impatrq/cnc_drawing_machine/boton de parada de emergencia/WhatsApp Image 2023-11-23 at 18.12.33.jpeg

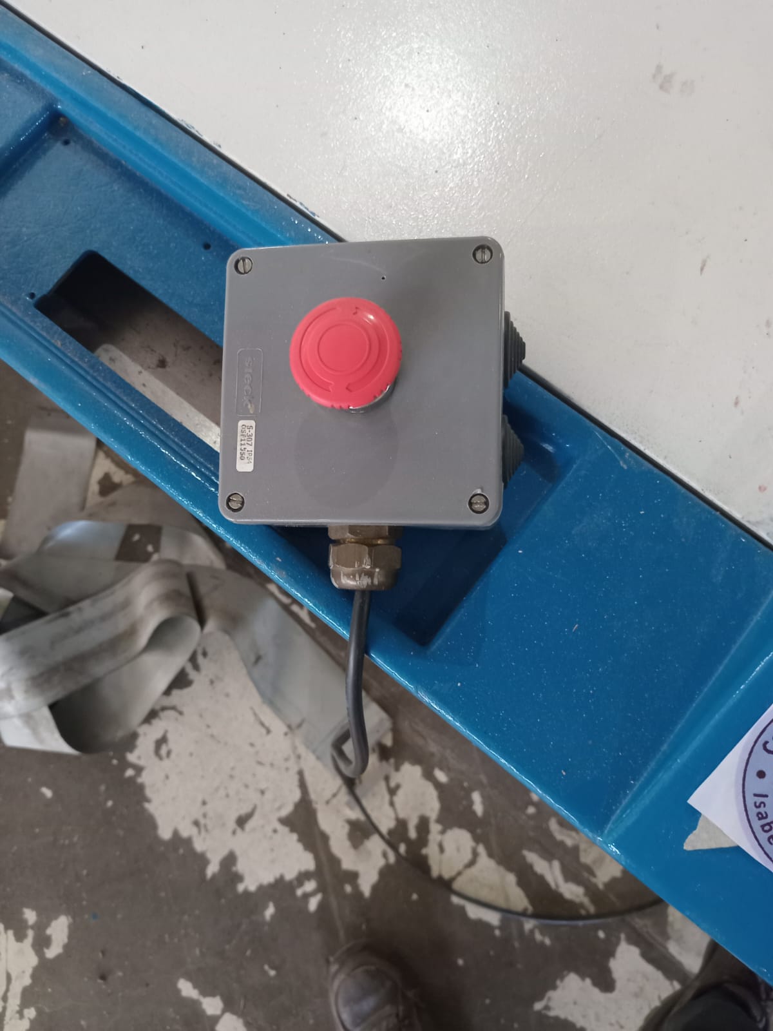
boton de parada de emergencia/WhatsApp Image 2023-11-23 at 18.12.33.jpeg
