impatrq/cnc_drawing_machine/Cortes y Grabados/cartel-zanik-mining.jpg

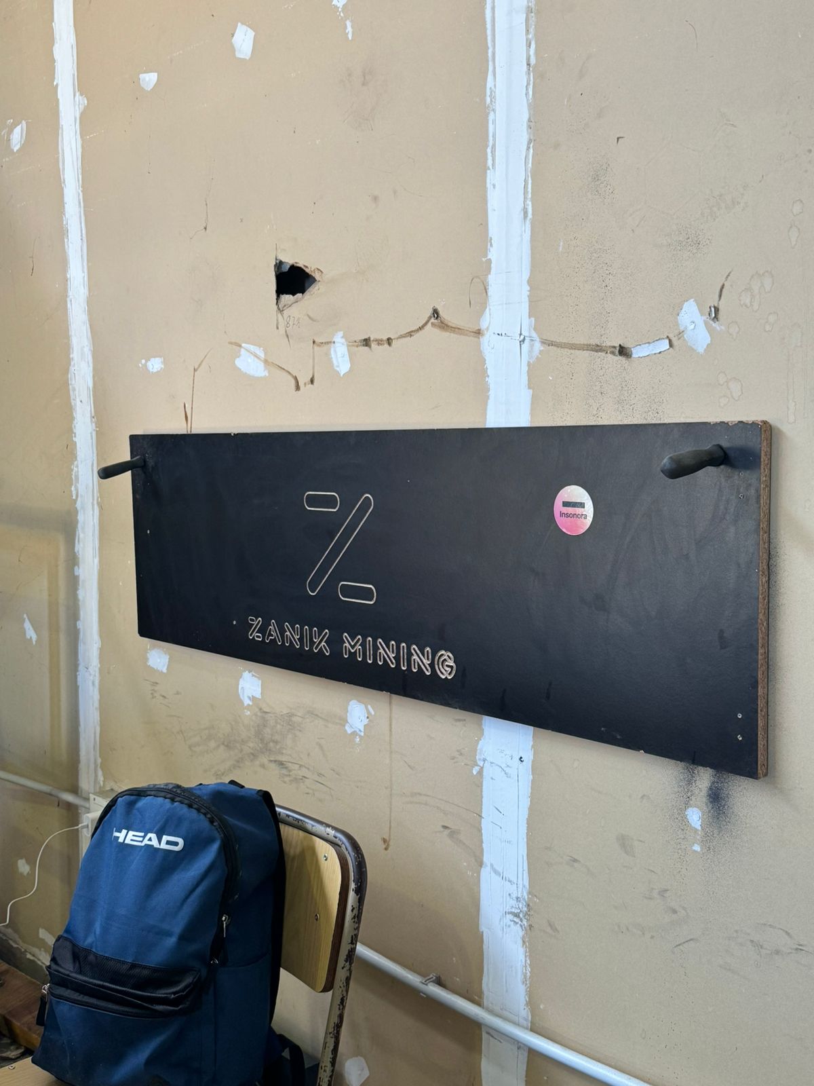
Cortes y Grabados/cartel-zanik-mining.jpg
