impatrq/cnc_drawing_machine/Cortes y Grabados/fluminense.jpg

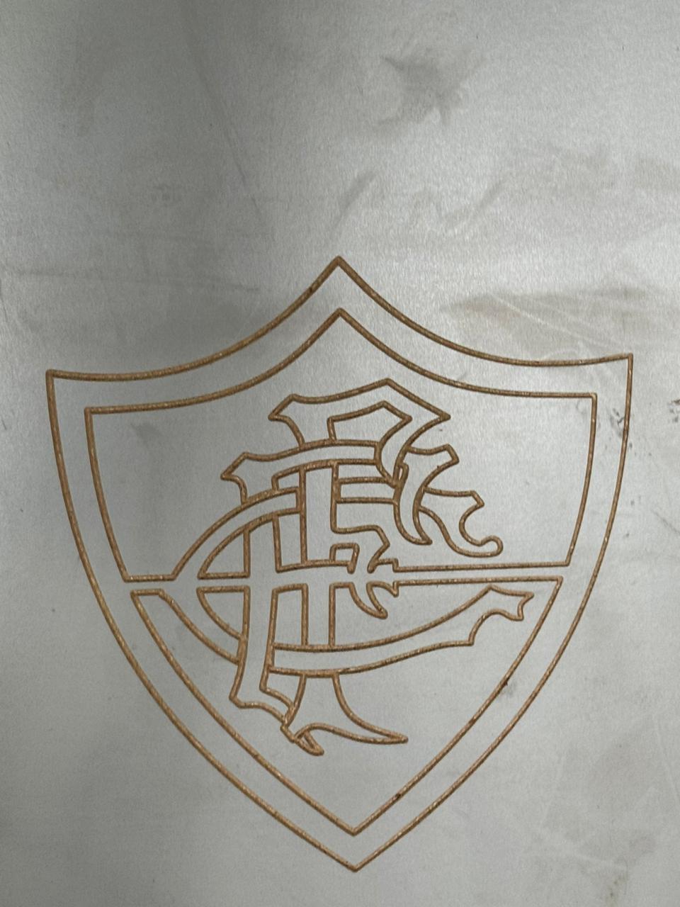
Cortes y Grabados/fluminense.jpg
