impatrq/cnc_drawing_machine/Cortes y Grabados/independiente .jpg

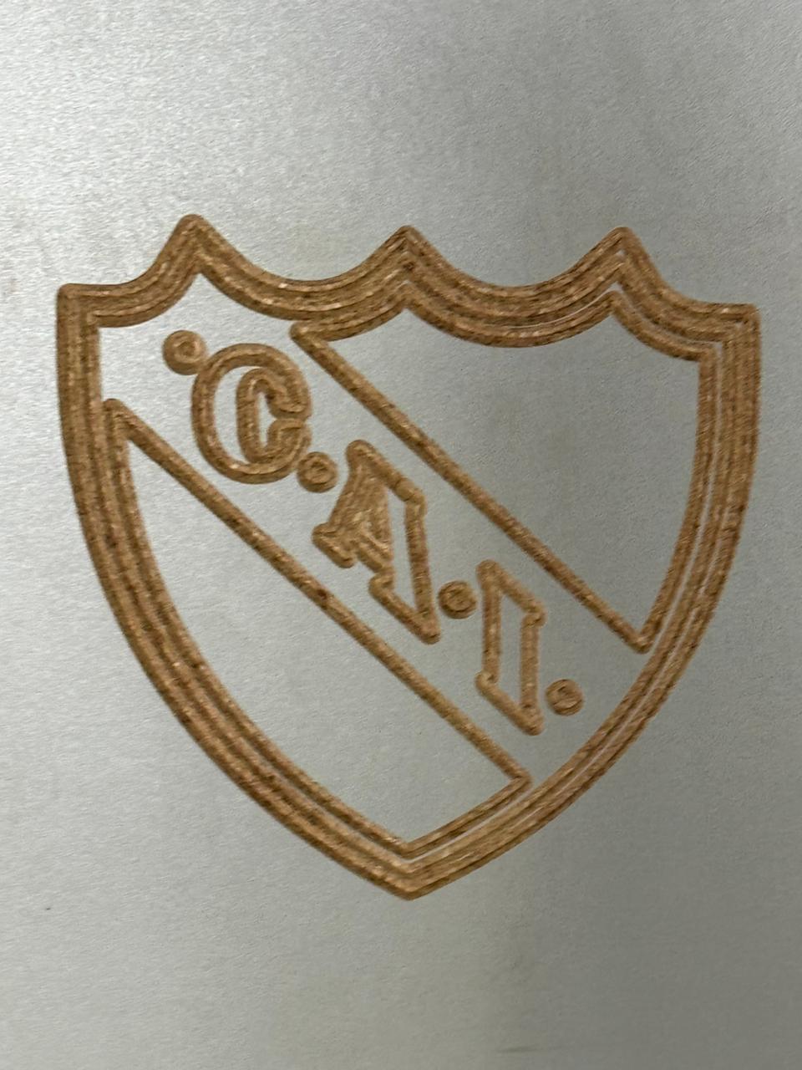
Cortes y Grabados/independiente .jpg
