impatrq/cnc_drawing_machine/Cortes y Grabados/mariposa.jpg

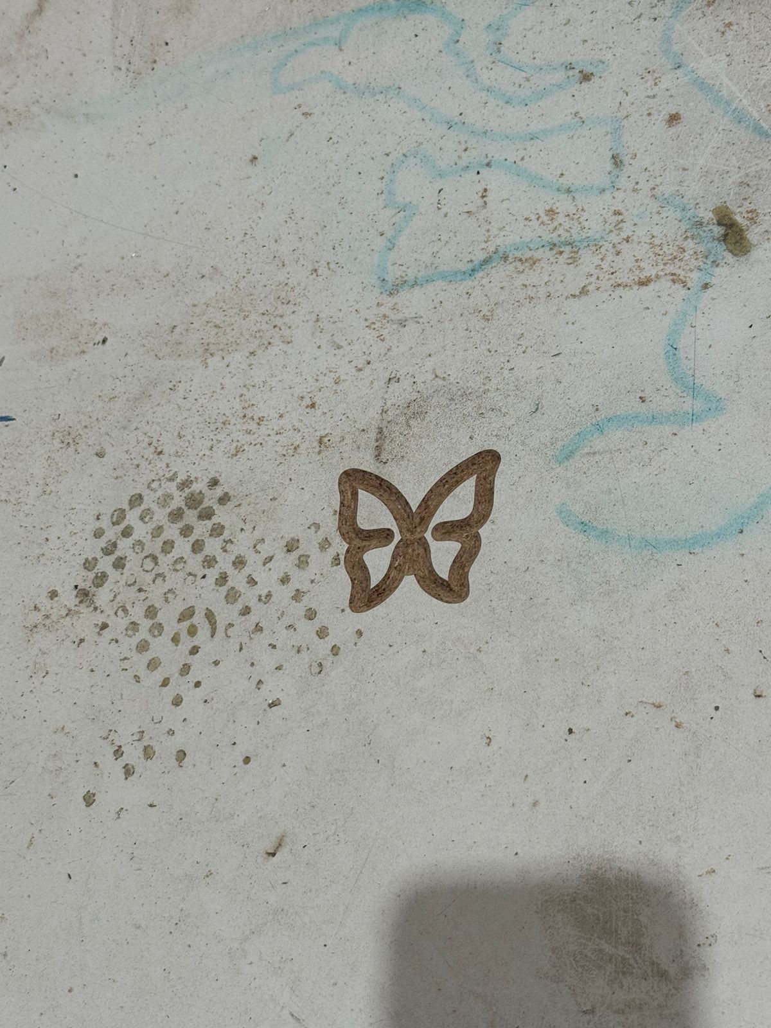
Cortes y Grabados/mariposa.jpg
