impatrq/cnc_drawing_machine/Cortes y Grabados/messi.jpg

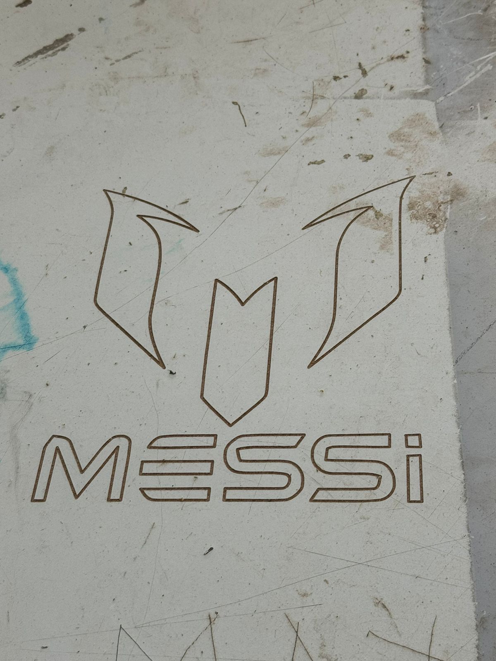
Cortes y Grabados/messi.jpg
