impatrq/cnc_drawing_machine/Cortes y Grabados/munay.jpg

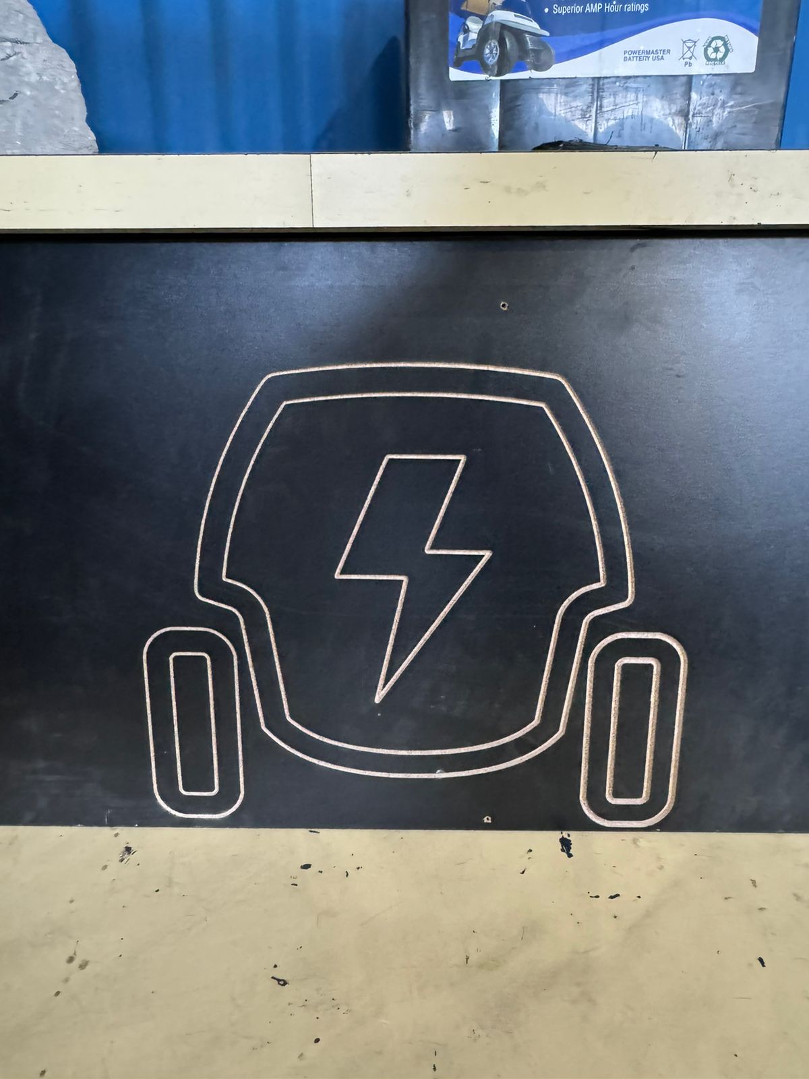
Cortes y Grabados/munay.jpg
