impatrq/cnc_drawing_machine/Cortes y Grabados/rick.jpg

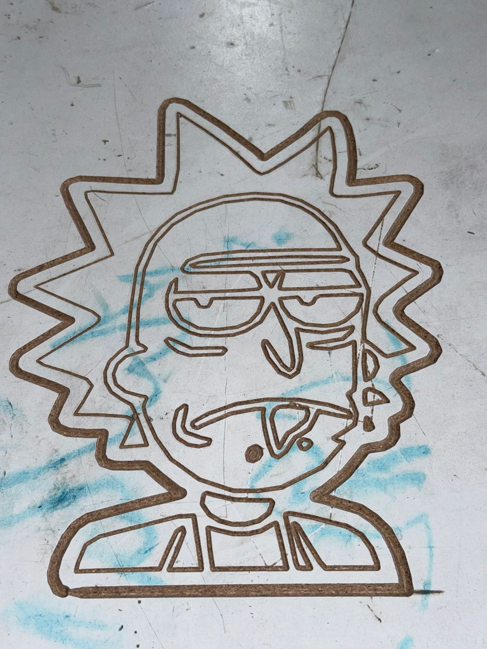
Cortes y Grabados/rick.jpg
