impatrq/cnc_drawing_machine/Cortes y Grabados/sonic.jpg

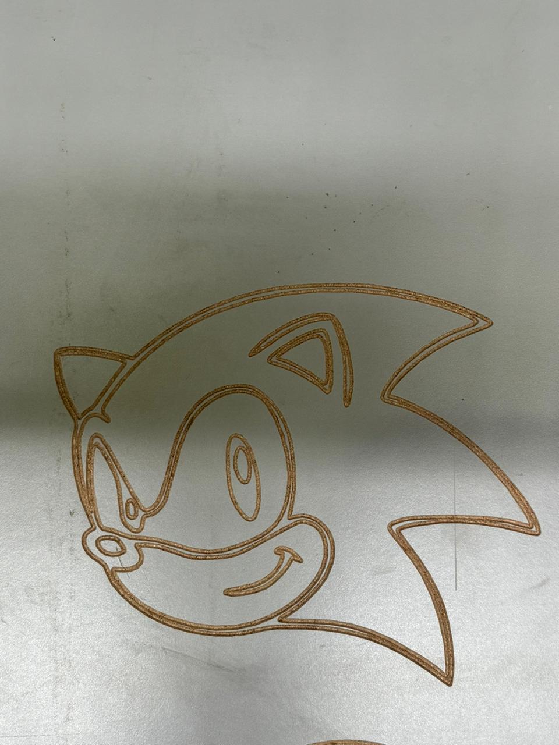
Cortes y Grabados/sonic.jpg
