impatrq/cnc_drawing_machine/Driver Modular/Driver Modular Tb6600 Settings.jpg

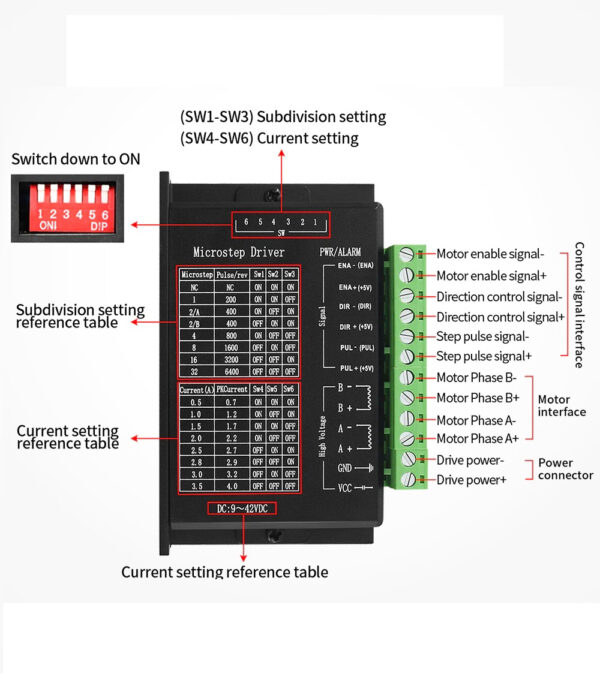
Driver Modular/Driver Modular Tb6600 Settings.jpg
