impatrq/cnc_drawing_machine/Driver Modular/Driver Modular Tb6600.png

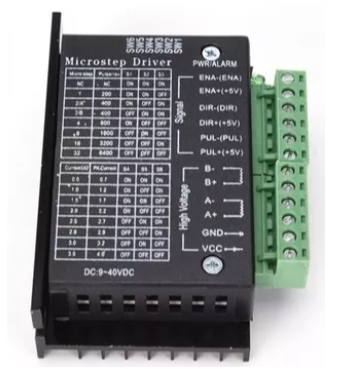
Driver Modular/Driver Modular Tb6600.png
