impatrq/cnc_drawing_machine/Driver Modular/drivers.jpg

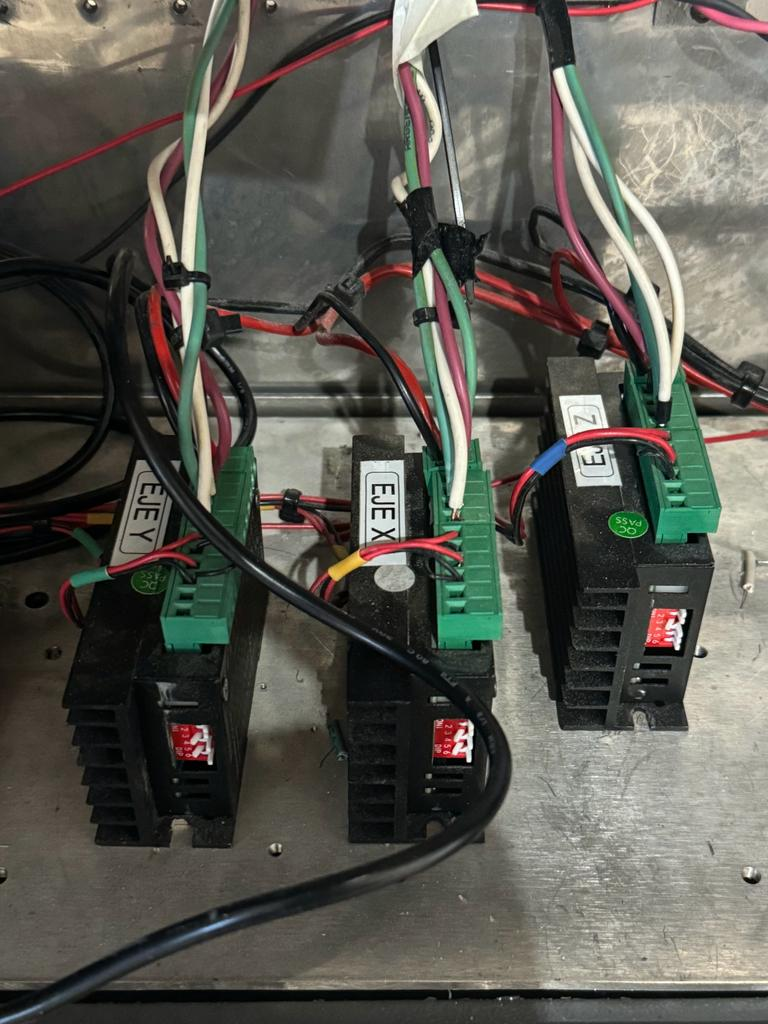
Driver Modular/drivers.jpg
