impatrq/cnc_drawing_machine/Eje X/Eje X conectado a su soporte.jpeg

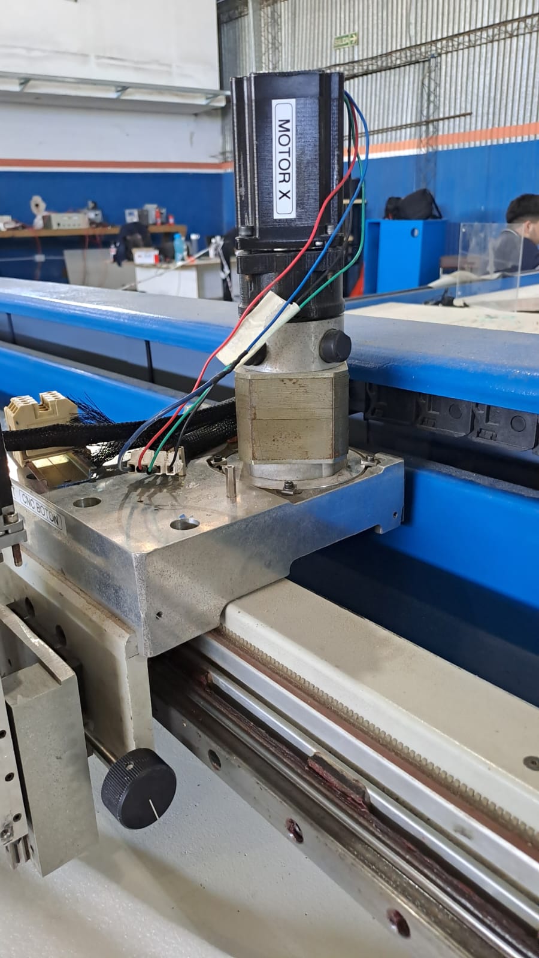
Eje X/Eje X conectado a su soporte.jpeg
