impatrq/cnc_drawing_machine/Eje X/Vista de lado del driver del Eje X.jpeg

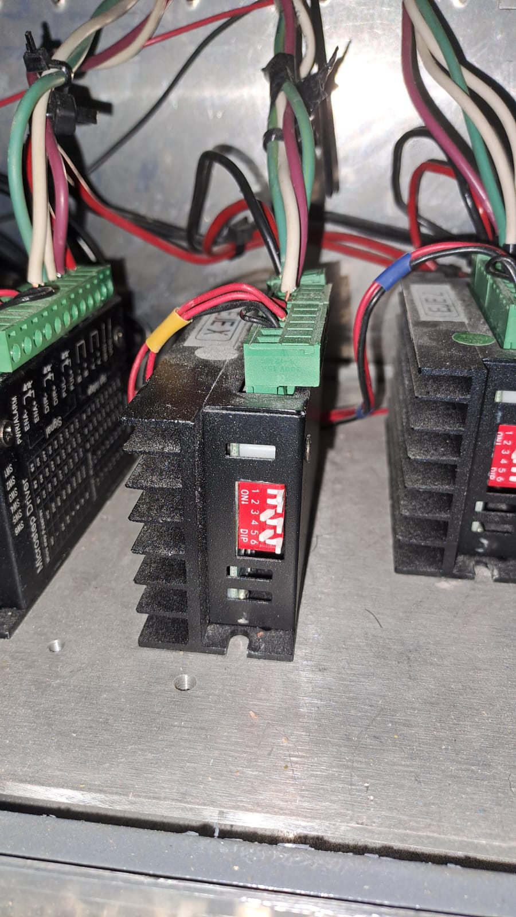
Eje X/Vista de lado del driver del Eje X.jpeg
