impatrq/cnc_drawing_machine/eje y/WhatsApp Image 2023-11-23 at 18.12.32 (1).jpeg

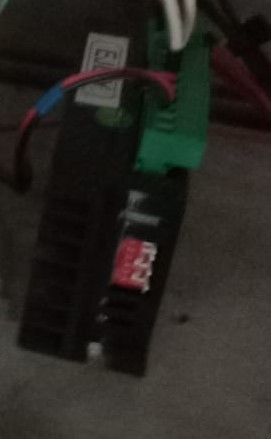
eje y/WhatsApp Image 2023-11-23 at 18.12.32 (1).jpeg
