impatrq/cnc_drawing_machine/eje y/WhatsApp Image 2023-11-24 at 00.11.37.jpeg

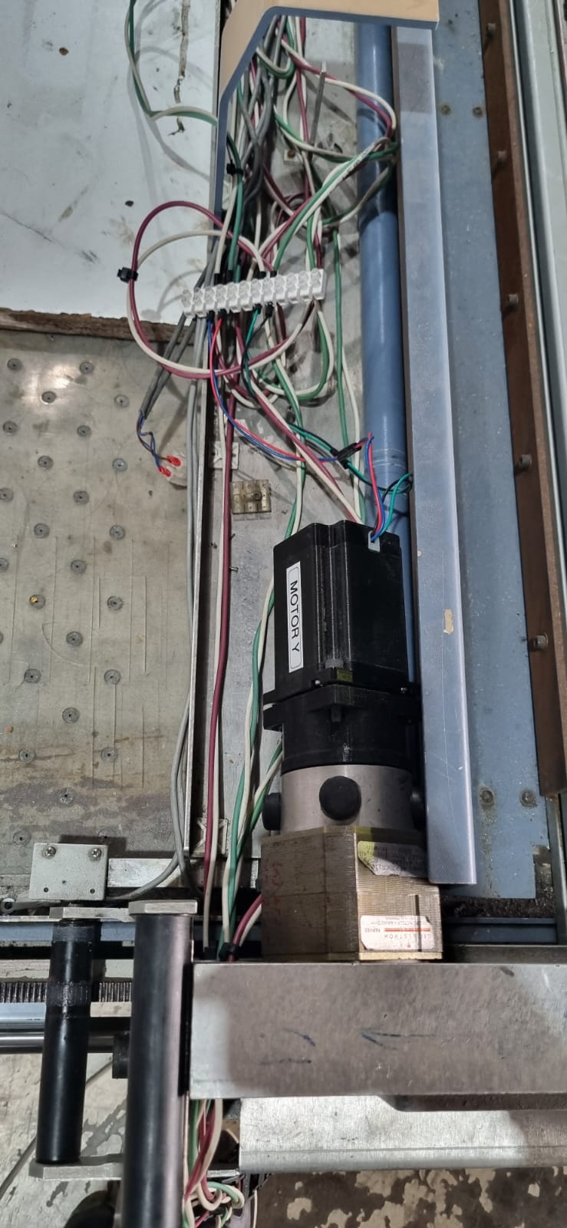
eje y/WhatsApp Image 2023-11-24 at 00.11.37.jpeg
