impatrq/cnc_drawing_machine/eje z/d.jpg

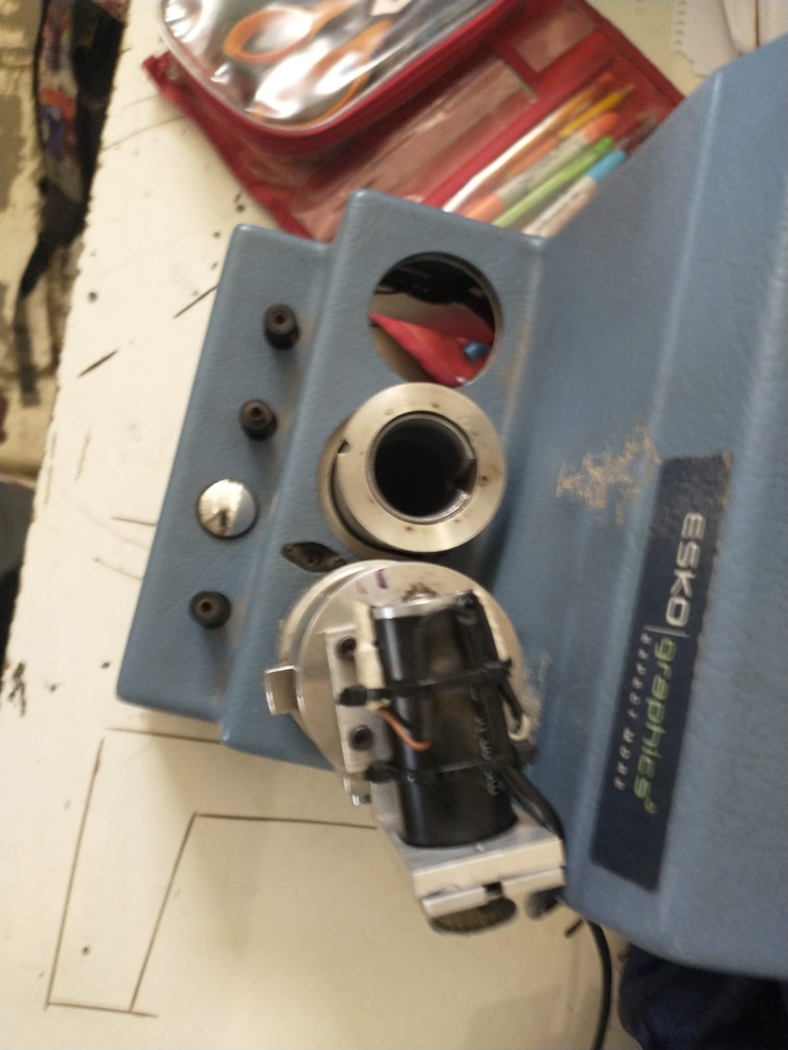
eje z/d.jpg
