impatrq/cnc_drawing_machine/eje z/parte movil eje z.PNG

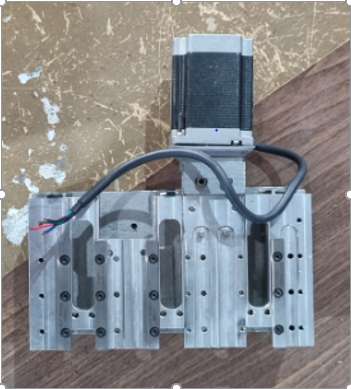
eje z/parte movil eje z.PNG
