impatrq/cnc_drawing_machine/eje z/WhatsApp Image 2023-11-23 at 18.12.32 (2).jpeg

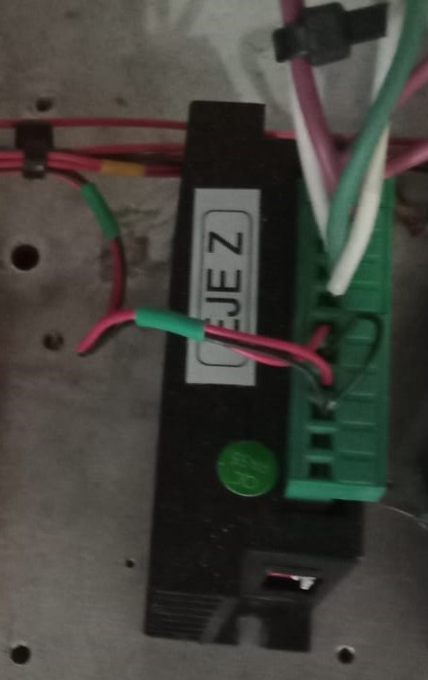
eje z/WhatsApp Image 2023-11-23 at 18.12.32 (2).jpeg
