impatrq/cnc_drawing_machine/eje z/WhatsApp Image 2023-11-24 at 00.47.14.jpeg

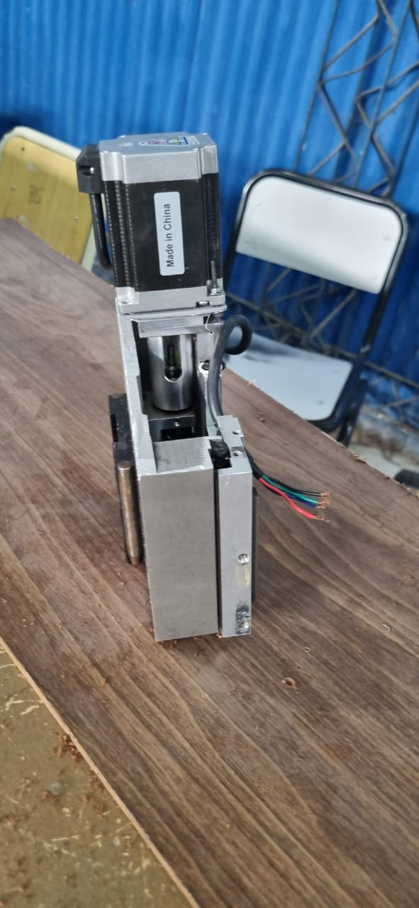
eje z/WhatsApp Image 2023-11-24 at 00.47.14.jpeg
