impatrq/cnc_drawing_machine/Esquema eléctrico del CNC/Esquema de CNC.jpg

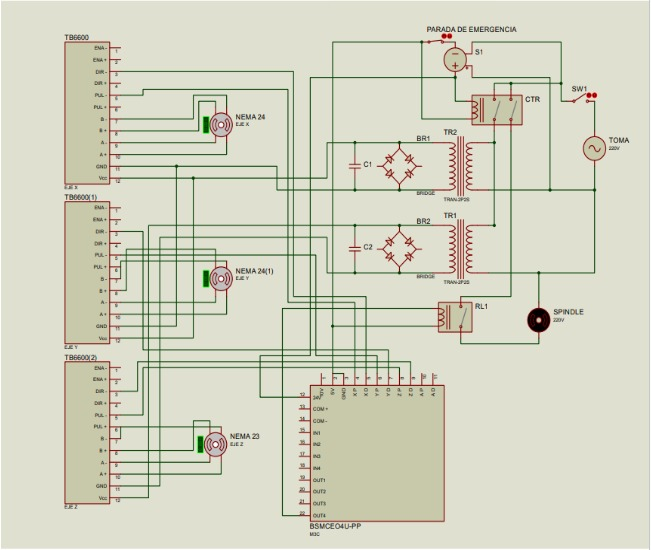
Esquema eléctrico del CNC/Esquema de CNC.jpg
