impatrq/cnc_drawing_machine/Esquema eléctrico del CNC/WhatsApp Image 2023-11-23 at 23.42.56 (1).jpeg

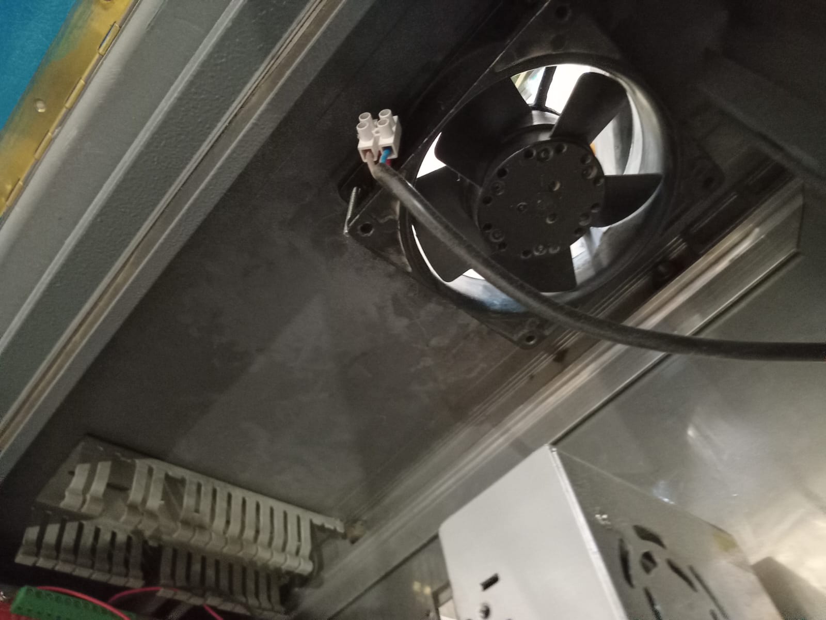
Esquema eléctrico del CNC/WhatsApp Image 2023-11-23 at 23.42.56 (1).jpeg
