impatrq/cnc_drawing_machine/Facturacion/Factura 1.png

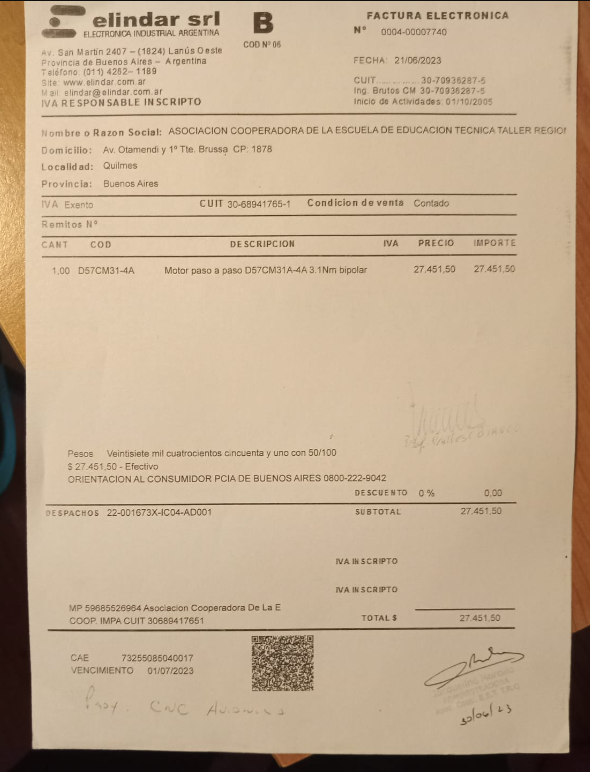
Facturacion/Factura 1.png
