impatrq/cnc_drawing_machine/Facturacion/Factura 2.png

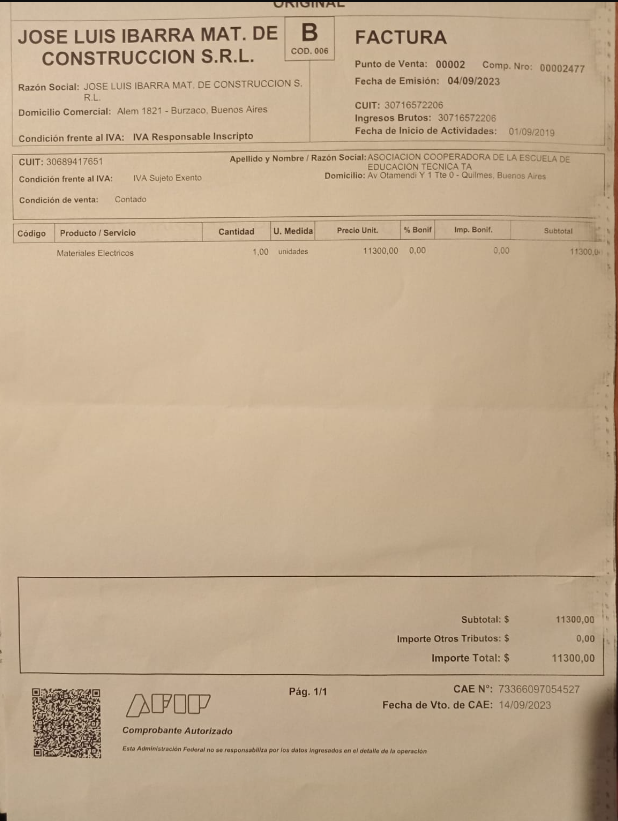
Facturacion/Factura 2.png
