impatrq/cnc_drawing_machine/Facturacion/Presupuesto 1.png

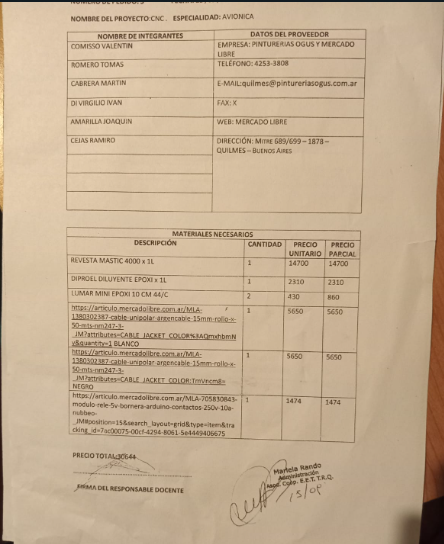
Facturacion/Presupuesto 1.png
