impatrq/cnc_drawing_machine/Facturacion/Presupuesto 2.png

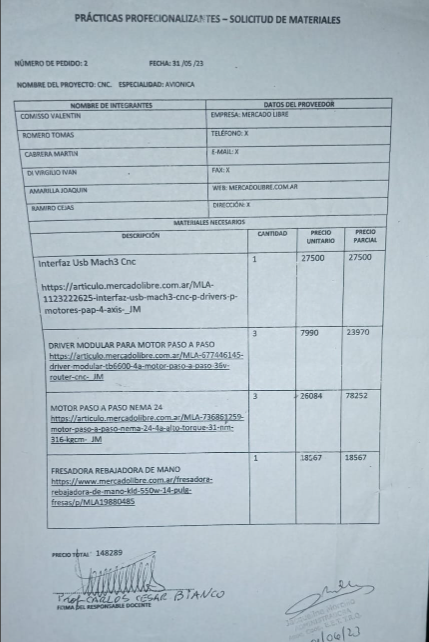
Facturacion/Presupuesto 2.png
