impatrq/cnc_drawing_machine/Facturacion/Presupuesto 3.png

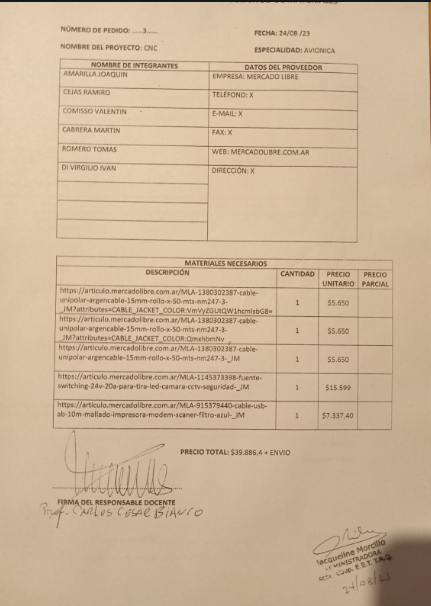
Facturacion/Presupuesto 3.png
