impatrq/cnc_drawing_machine/Fresadora/config_fresadora.PNG

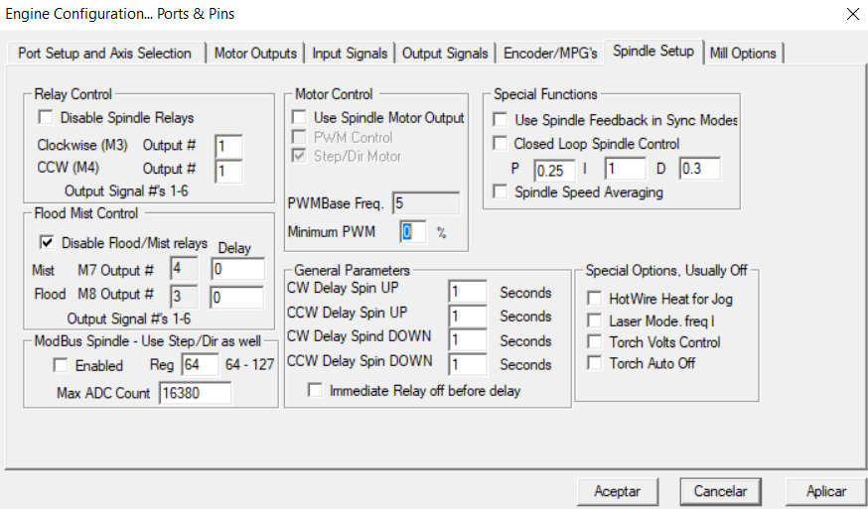
Fresadora/config_fresadora.PNG
