impatrq/cnc_drawing_machine/Fresadora/pins_fresadora.PNG

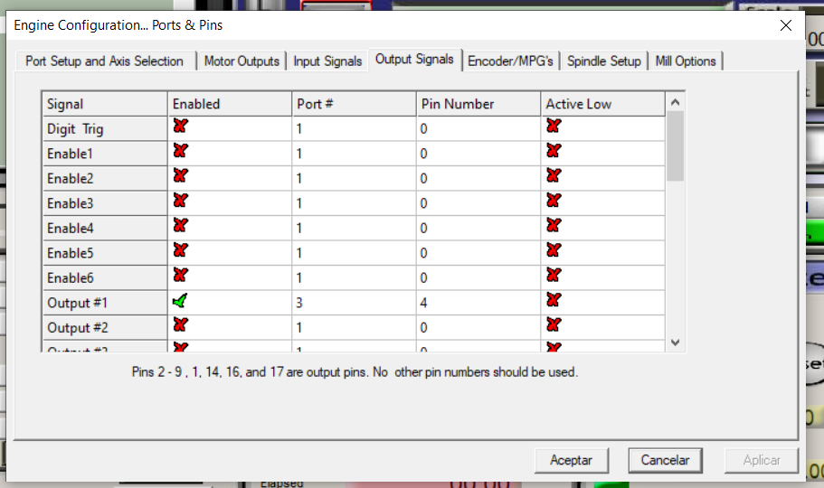
Fresadora/pins_fresadora.PNG
