impatrq/cnc_drawing_machine/Fresadora/rele y contactor.jpeg

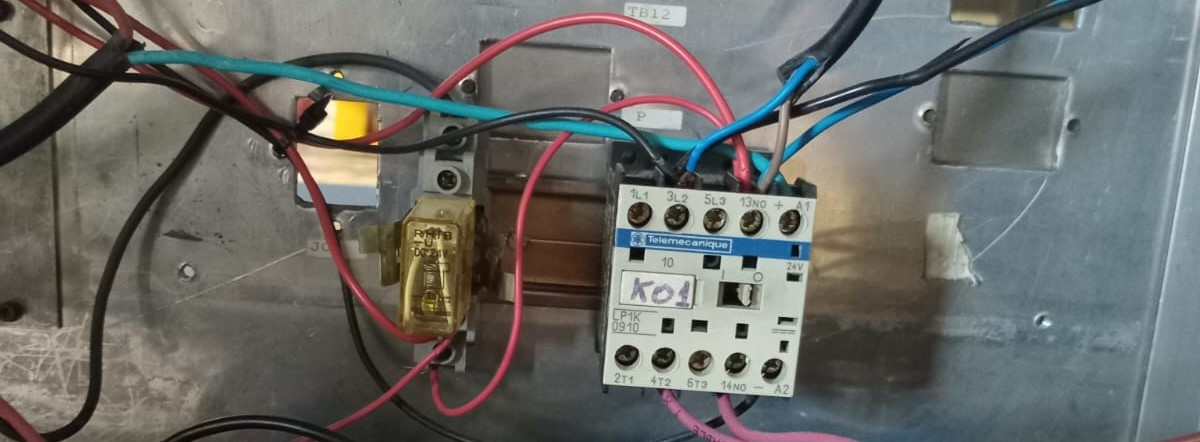
Fresadora/rele y contactor.jpeg
