impatrq/cnc_drawing_machine/Fresadora/WhatsApp Image 2023-11-23 at 23.48.01.jpeg

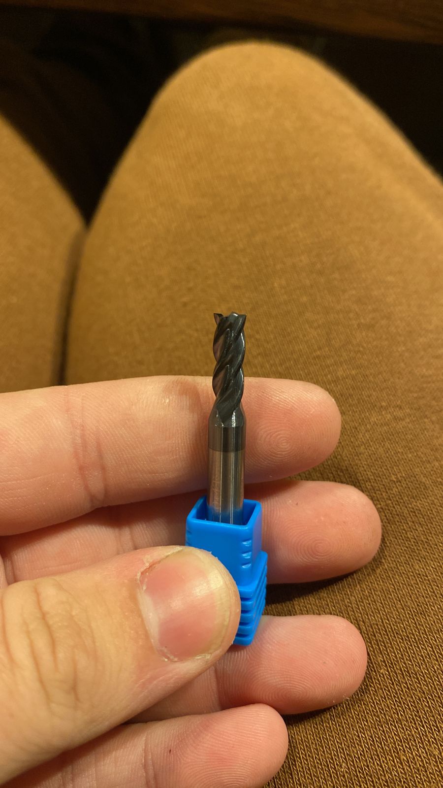
Fresadora/WhatsApp Image 2023-11-23 at 23.48.01.jpeg
