impatrq/cnc_drawing_machine/Fresadora/WhatsApp Image 2023-11-23 at 23.52.09.jpeg

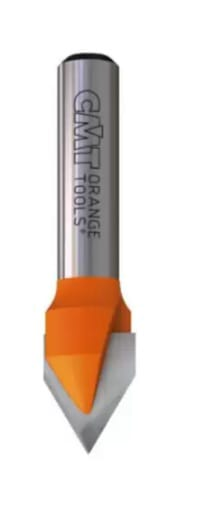
Fresadora/WhatsApp Image 2023-11-23 at 23.52.09.jpeg
