impatrq/cnc_drawing_machine/fuente/WhatsApp Image 2023-11-23 at 18.12.32.jpeg

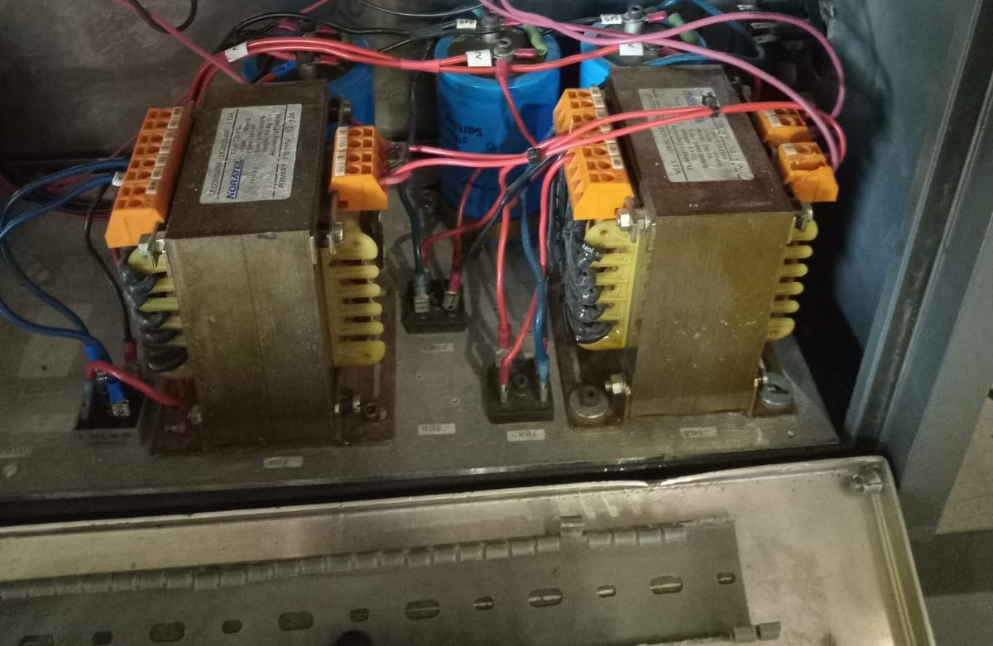
fuente/WhatsApp Image 2023-11-23 at 18.12.32.jpeg
