impatrq/cnc_drawing_machine/Interfaz-RNR/conexion-fresa.jpg

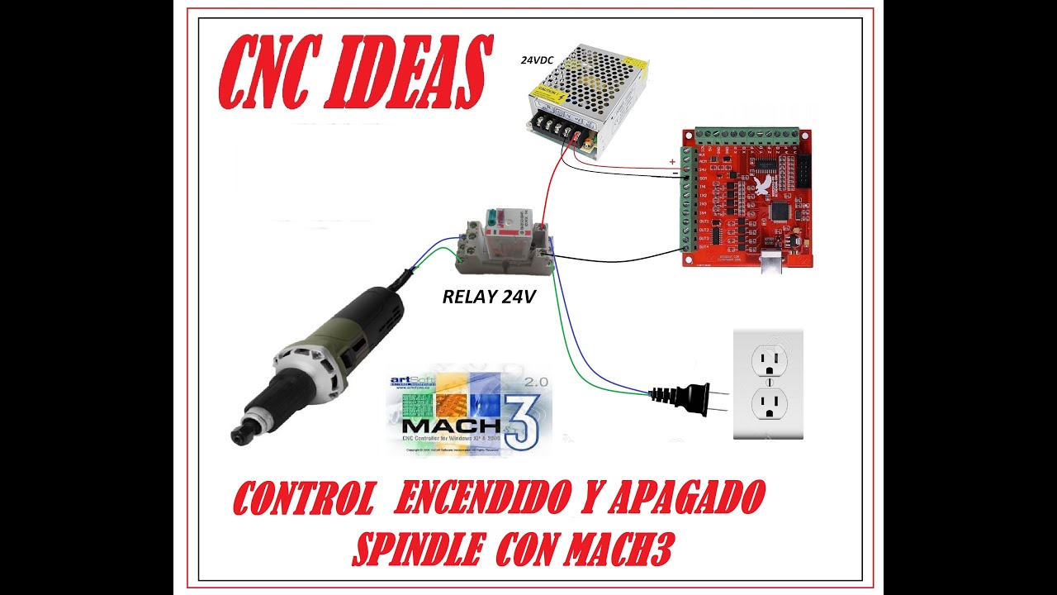
Interfaz-RNR/conexion-fresa.jpg
