impatrq/cnc_drawing_machine/Interfaz-RNR/conexion-solo-driver-e-motores.jpg

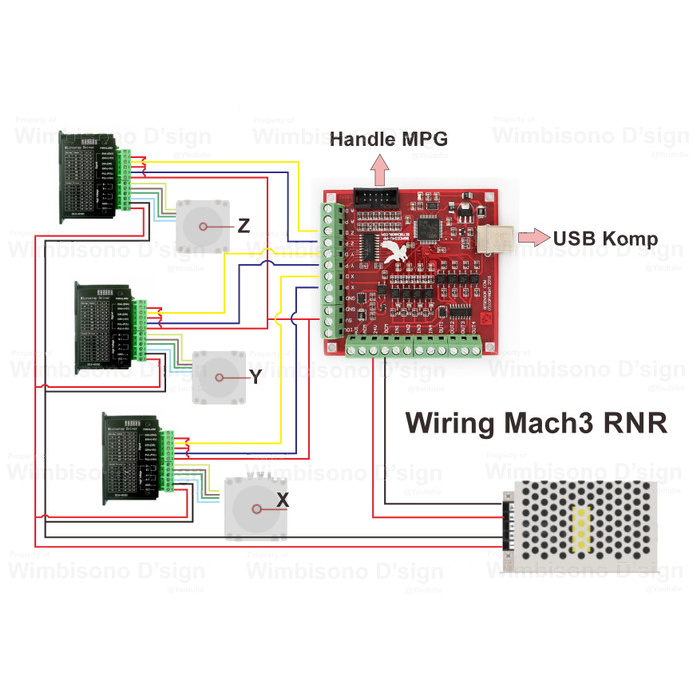
Interfaz-RNR/conexion-solo-driver-e-motores.jpg
