impatrq/cnc_drawing_machine/Interfaz-RNR/Esquema de la placa de interfaz.PNG

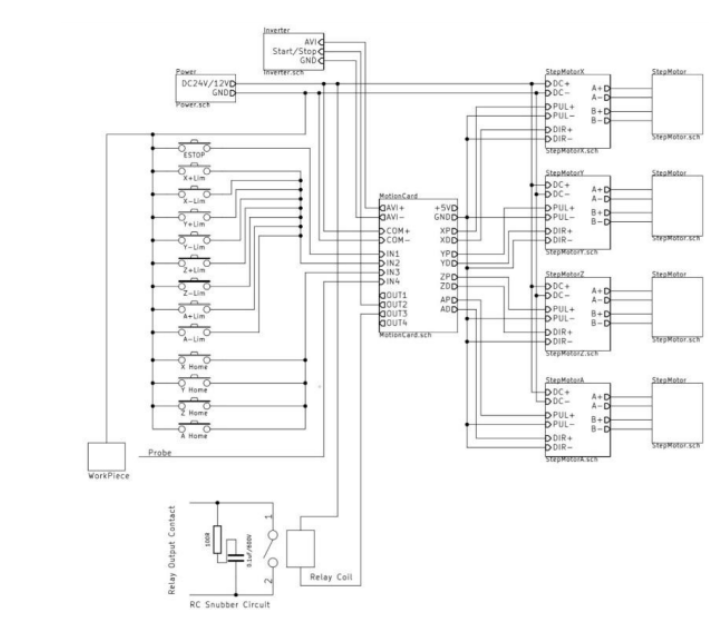
Interfaz-RNR/Esquema de la placa de interfaz.PNG
