impatrq/cnc_drawing_machine/Interfaz-RNR/multiples-posibles-conexiones.jpg

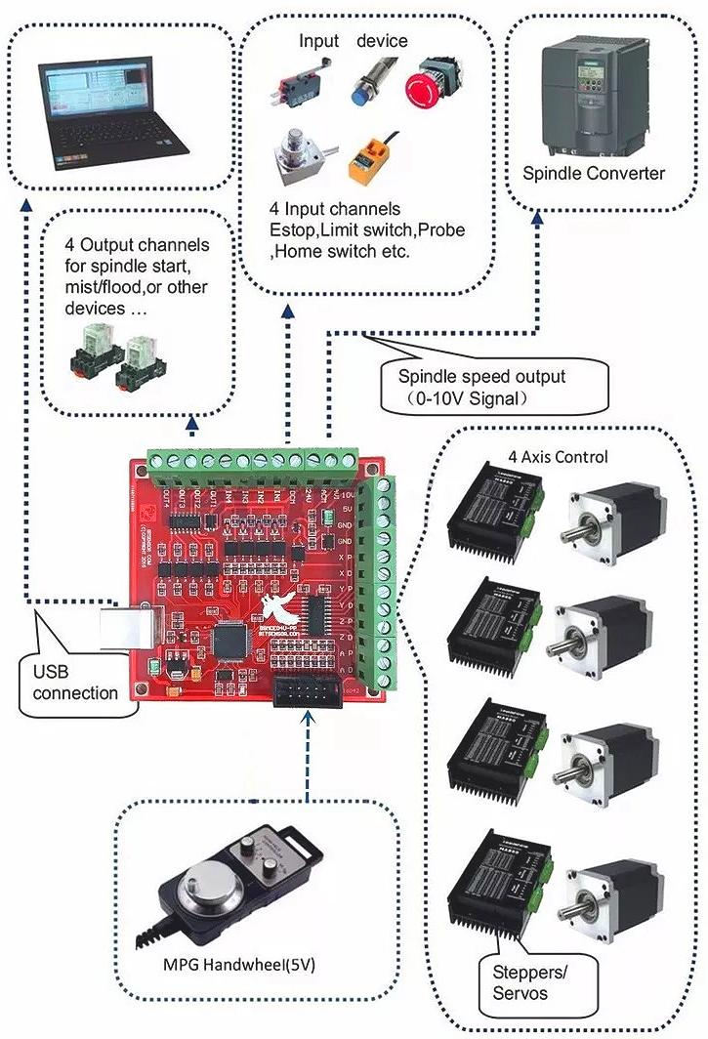
Interfaz-RNR/multiples-posibles-conexiones.jpg
