impatrq/cnc_drawing_machine/Interfaz-RNR/rnr-info.png

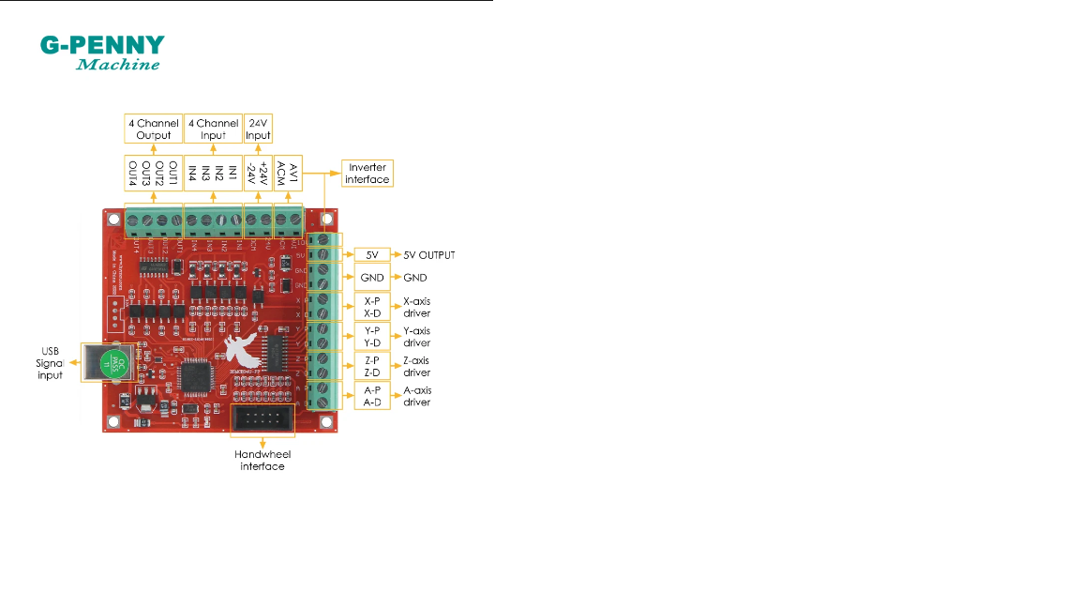
Interfaz-RNR/rnr-info.png
