impatrq/cnc_drawing_machine/Interfaz-RNR/rnr.jpg

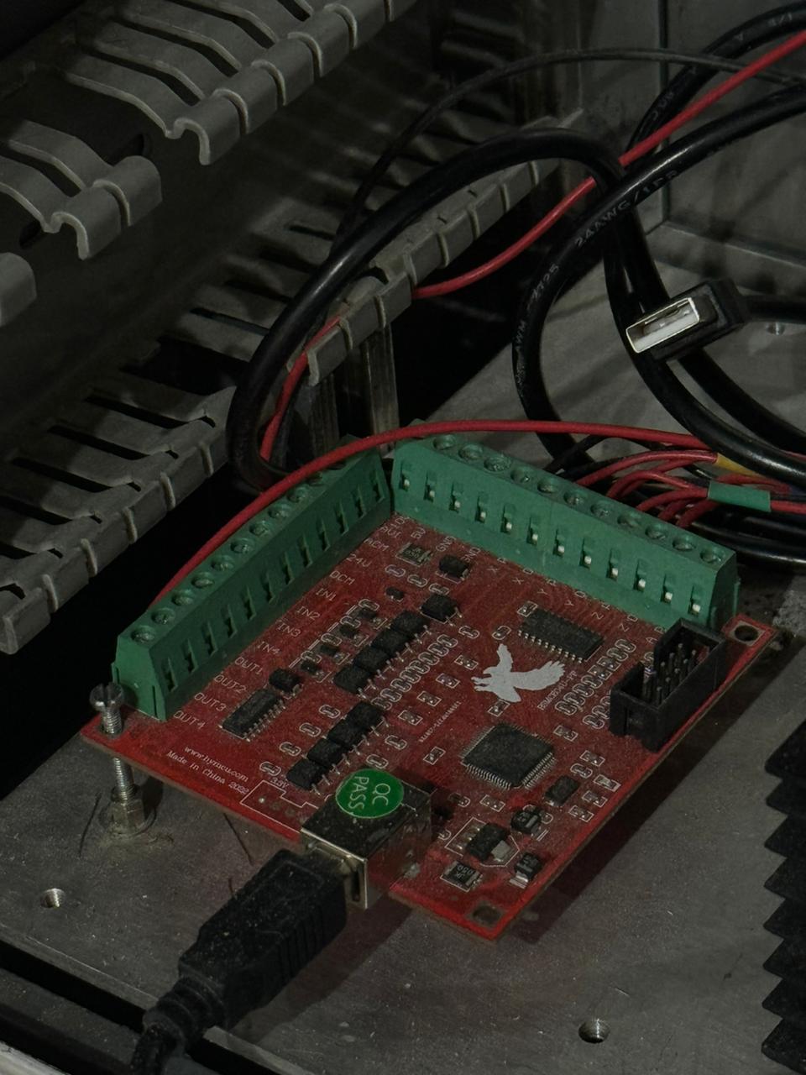
Interfaz-RNR/rnr.jpg
