impatrq/cnc_drawing_machine/Restauración/Alimentación/Circuito electrico antes (1).PNG

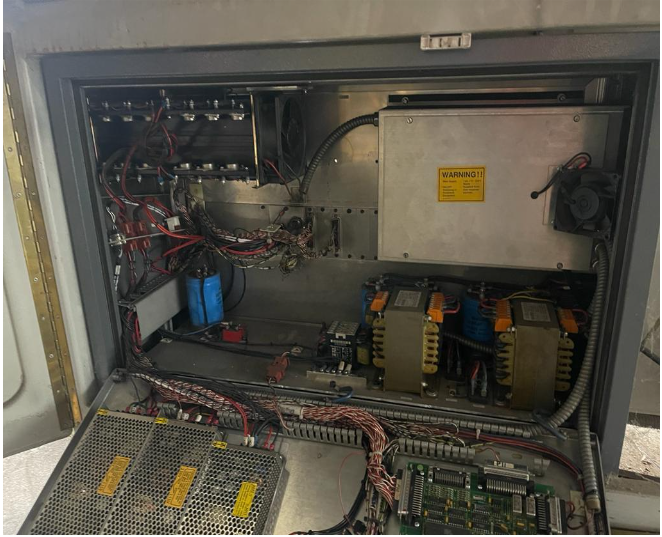
Restauración/Alimentación/Circuito electrico antes (1).PNG
