impatrq/cnc_drawing_machine/Restauración/Alimentación/Circuito electrico Despues.PNG

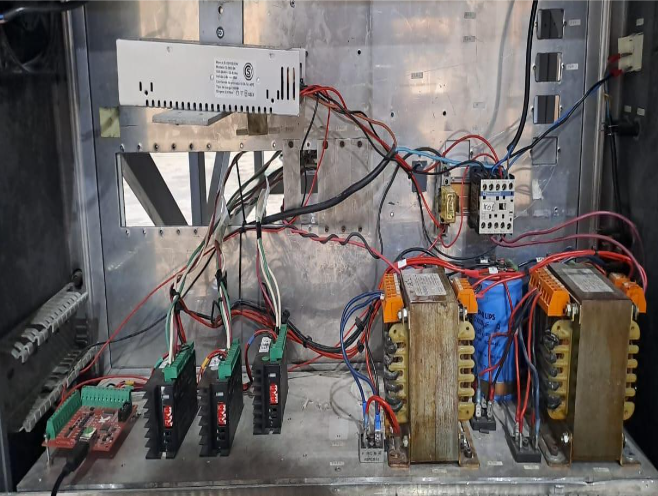
Restauración/Alimentación/Circuito electrico Despues.PNG
