impatrq/cnc_drawing_machine/Restauración/Base CNC/Base Delantera del CNC (2).png

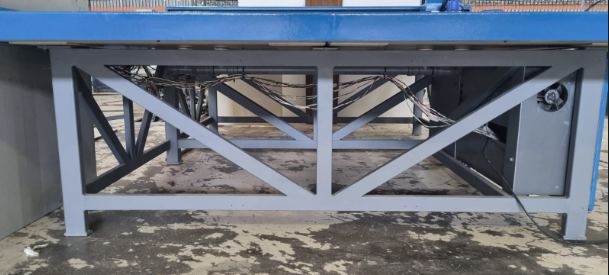
Restauración/Base CNC/Base Delantera del CNC (2).png
