impatrq/cnc_drawing_machine/Restauración/Base CNC/Base Trasera del CNC.png

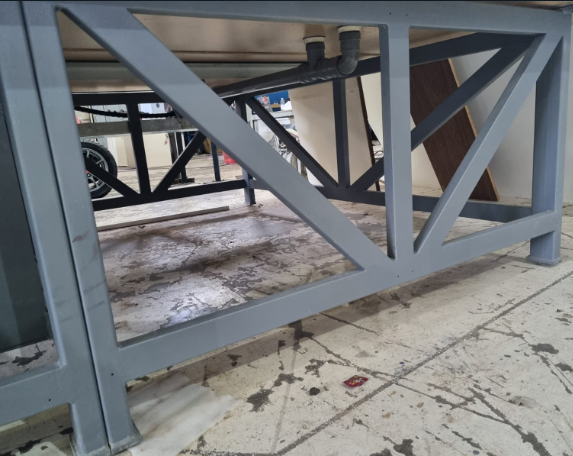
Restauración/Base CNC/Base Trasera del CNC.png
