impatrq/cnc_drawing_machine/Restauración/Base CNC/Gabinete.png

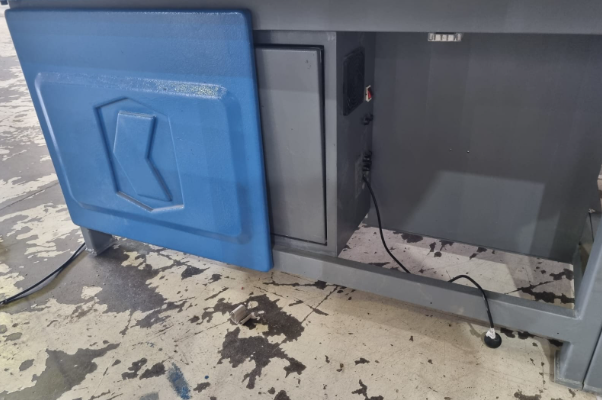
Restauración/Base CNC/Gabinete.png
