impatrq/cnc_drawing_machine/Restauración/Carcasa_eje_x/CARCASA PROTECTORA DEL DE PASO A PASO EJE X RENOVADA.png

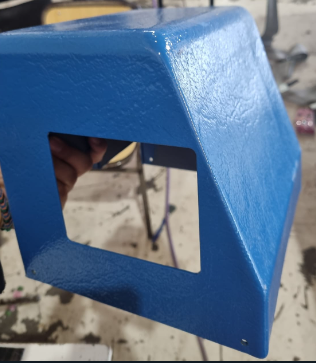
Restauración/Carcasa_eje_x/CARCASA PROTECTORA DEL DE PASO A PASO EJE X RENOVADA.png
