impatrq/cnc_drawing_machine/Restauración/Carcasa_eje_x/CARCASA PROTECTORA EJE X.png

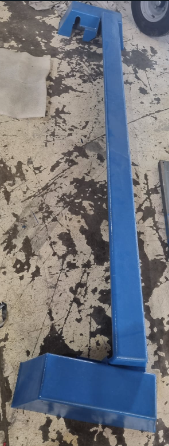
Restauración/Carcasa_eje_x/CARCASA PROTECTORA EJE X.png
