impatrq/cnc_drawing_machine/Restauración/Carcasa_eje_x/CARCASAS DE EJE X RESTAURADAS.png

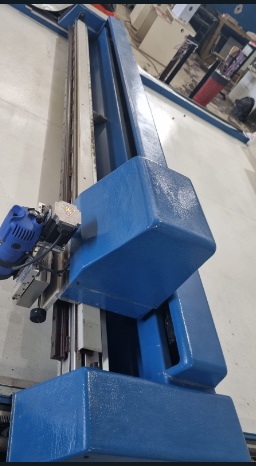
Restauración/Carcasa_eje_x/CARCASAS DE EJE X RESTAURADAS.png
