impatrq/cnc_drawing_machine/Restauración/Carcasa_eje_x/eje_x_pre_restauracion .jpg

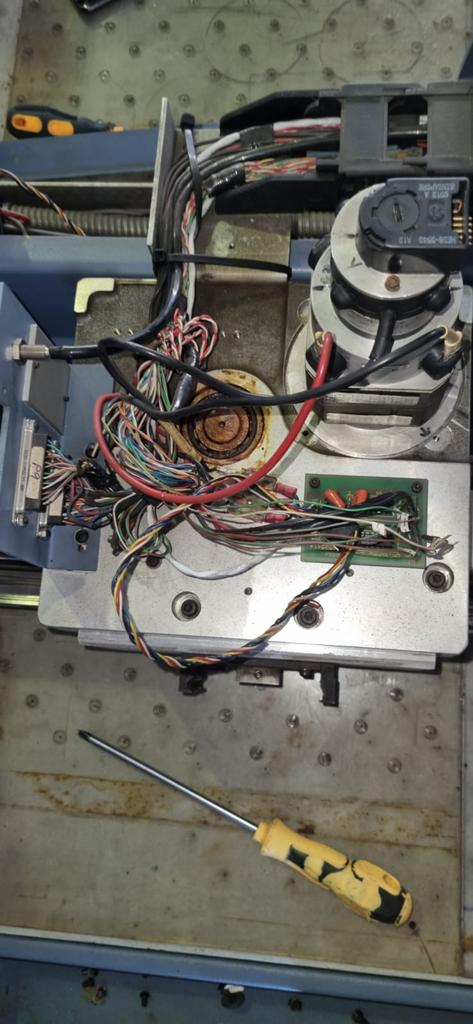
Restauración/Carcasa_eje_x/eje_x_pre_restauracion .jpg
