impatrq/cnc_drawing_machine/Restauración/Proteccion de Rieles/PLACAS FRONTALES DE RIELES.png

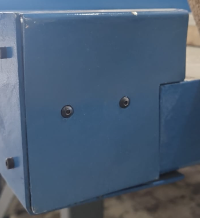
Restauración/Proteccion de Rieles/PLACAS FRONTALES DE RIELES.png
