impatrq/cnc_drawing_machine/Restauración/Proteccion de Rieles/PLACAS INTERIORES DE RIELES.png

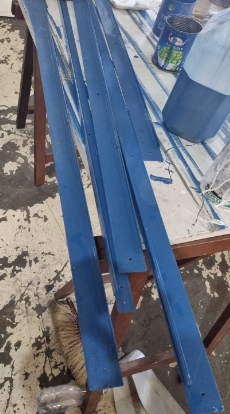
Restauración/Proteccion de Rieles/PLACAS INTERIORES DE RIELES.png
