impatrq/cnc_drawing_machine/Servo-Motores y Paso a Paso/Motor Paso A Paso Nema 23.png

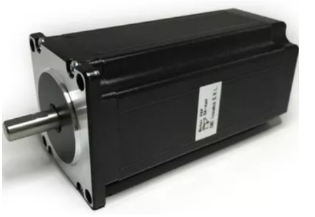
Servo-Motores y Paso a Paso/Motor Paso A Paso Nema 23.png
