impatrq/cnc_drawing_machine/Servo-Motores y Paso a Paso/Motor Paso A Paso Nema 24.png

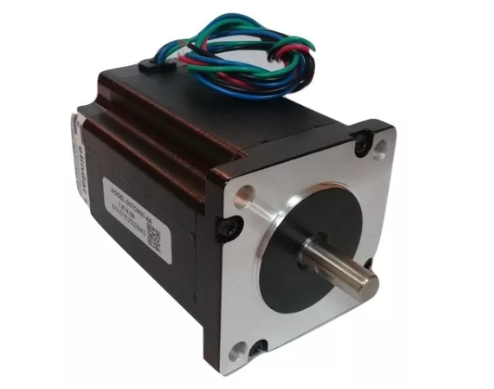
Servo-Motores y Paso a Paso/Motor Paso A Paso Nema 24.png
