impatrq/cnc_drawing_machine/Servo-Motores y Paso a Paso/Servo-Motor y Paso a Paso Conectado.jpeg

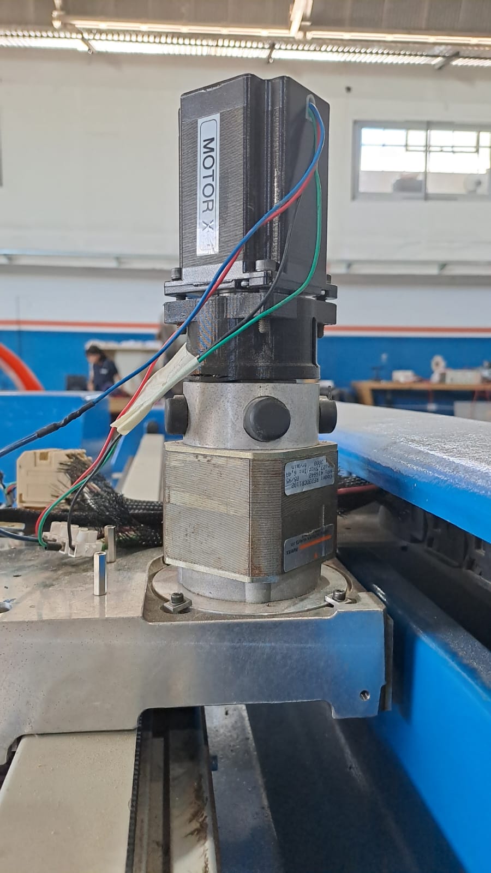
Servo-Motores y Paso a Paso/Servo-Motor y Paso a Paso Conectado.jpeg
