impatrq/cnc_drawing_machine/Servo-Motores y Paso a Paso/Servo-Motores.jpeg

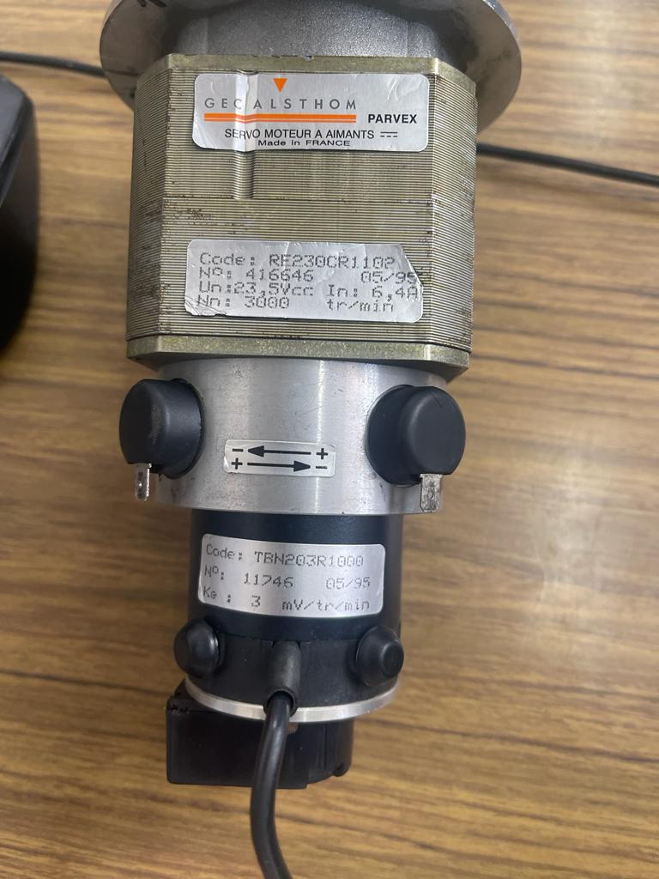
Servo-Motores y Paso a Paso/Servo-Motores.jpeg
