impatrq/cnc_drawing_machine/Soporte Cadena portacables/1.jpg

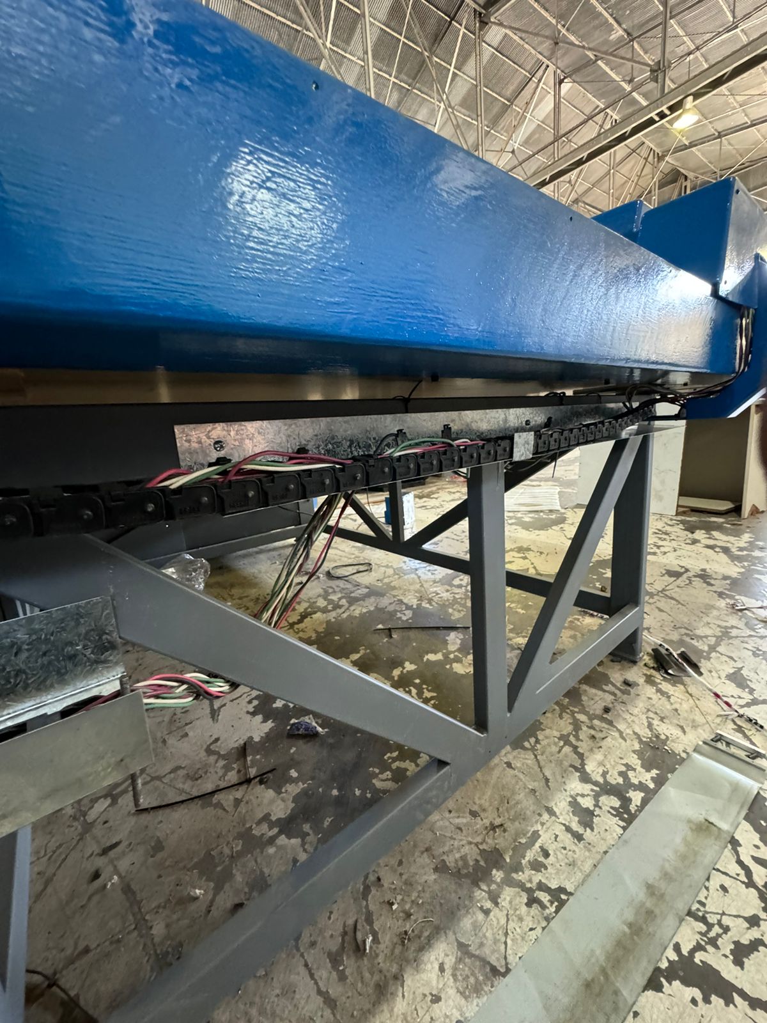
Soporte Cadena portacables/1.jpg
