impatrq/cnc_drawing_machine/Soporte Cadena portacables/2.jpg

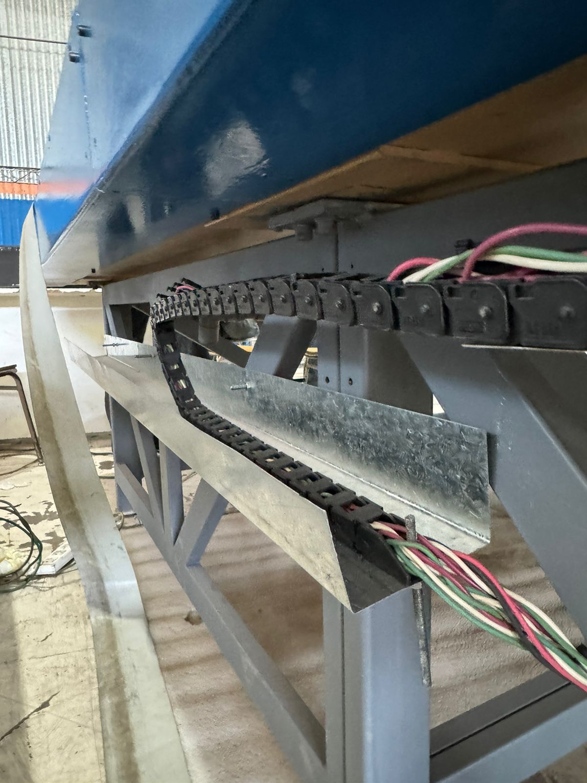
Soporte Cadena portacables/2.jpg
