impatrq/cnc_drawing_machine/Soporte Cadena portacables/3.jpg

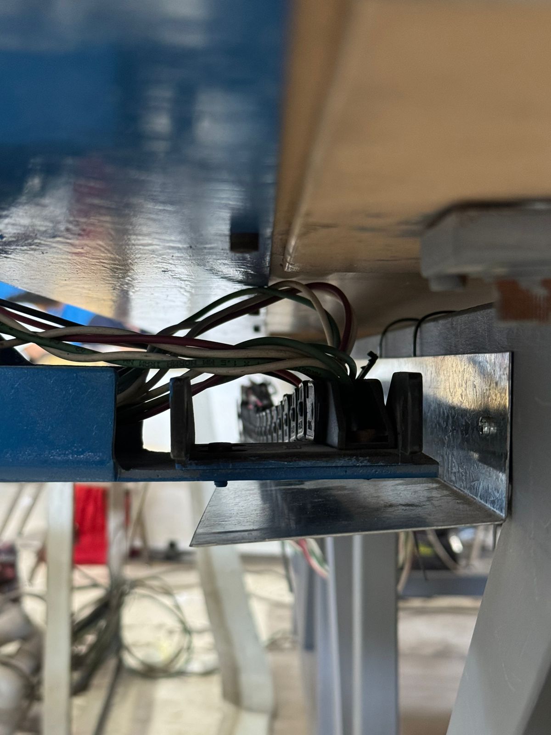
Soporte Cadena portacables/3.jpg
