impatrq/cnc_drawing_machine/Soporte Cadena portacables/4.jpg

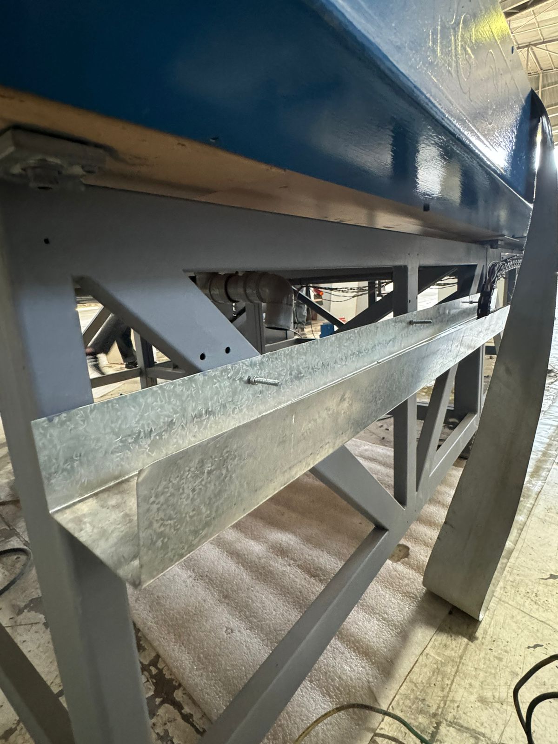
Soporte Cadena portacables/4.jpg
