impatrq/cnc_drawing_machine/Soporte Cadena portacables/soporte_cadena.jpg

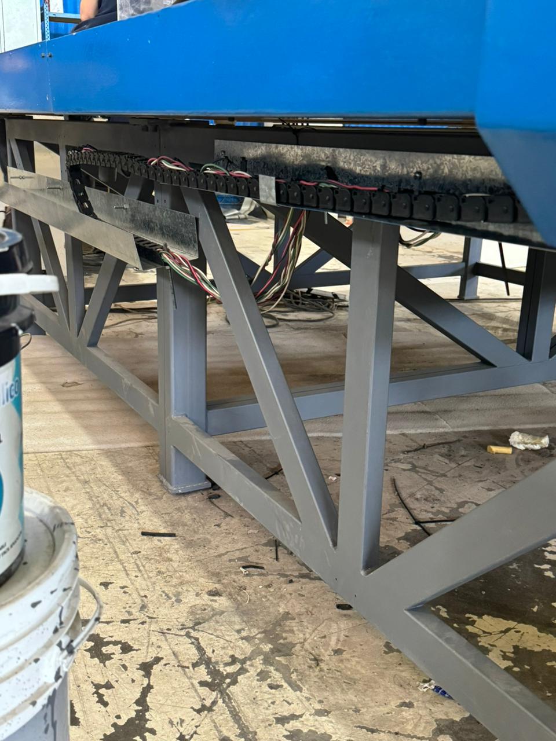
Soporte Cadena portacables/soporte_cadena.jpg
