impatrq/cnc_drawing_machine/Dibujos_dxf/cara.dxf

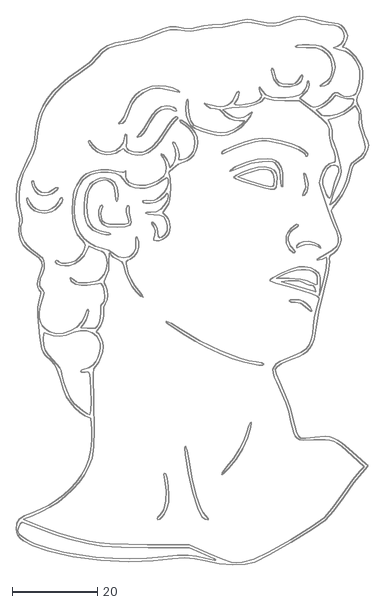
[picture p98: CAD file, 2023-11-14]
Dibujos_dxf/cara.dxf
82.9 x 129.0
