impatrq/cnc_drawing_machine/Dibujos_dxf/casco.dxf

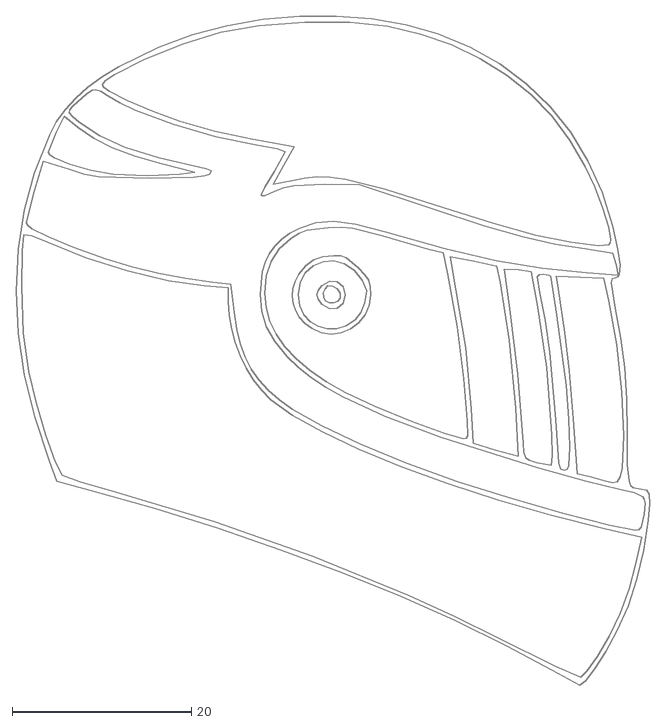
[picture p99: CAD file, 2023-11-14]
Dibujos_dxf/casco.dxf
70.7 x 74.7
