impatrq/cnc_drawing_machine/Dibujos_dxf/flash.dxf

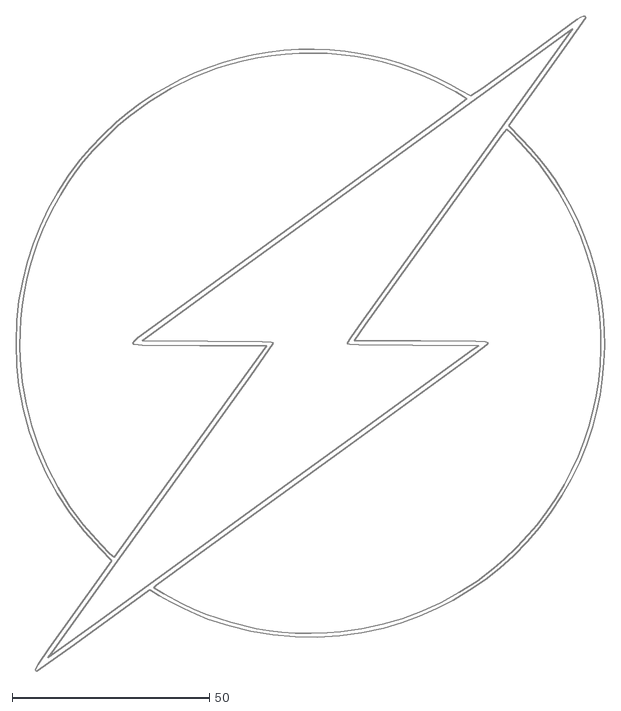
[picture p100: CAD file, 2023-11-14]
Dibujos_dxf/flash.dxf
149.1 x 166.0
