impatrq/cnc_drawing_machine/Dibujos_dxf/sony.dxf

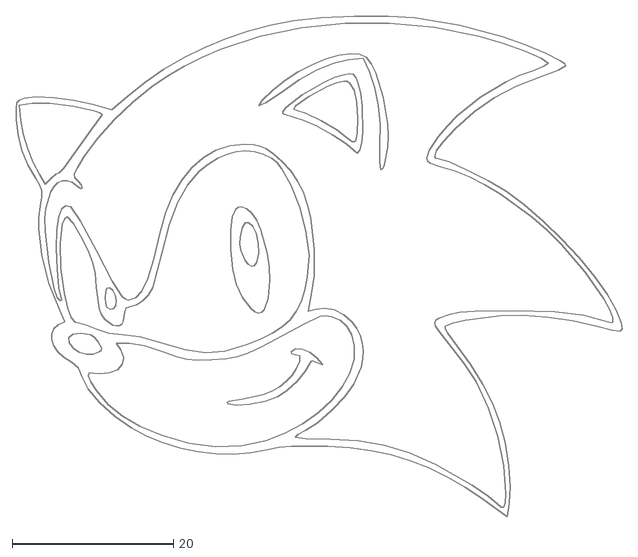
[picture p101: CAD file, 2023-11-14]
Dibujos_dxf/sony.dxf
75.2 x 62.1
