impatrq/cnc_drawing_machine/Dibujos_dxf/impa.dxf

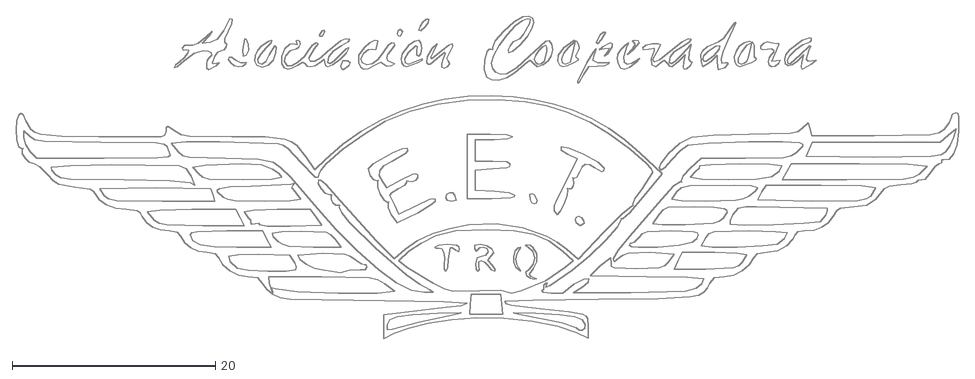
[picture p102: CAD file, 2023-11-14]
Dibujos_dxf/impa.dxf
92.8 x 31.7
