impatrq/cnc_drawing_machine/Dibujos_dxf/cartman.dxf

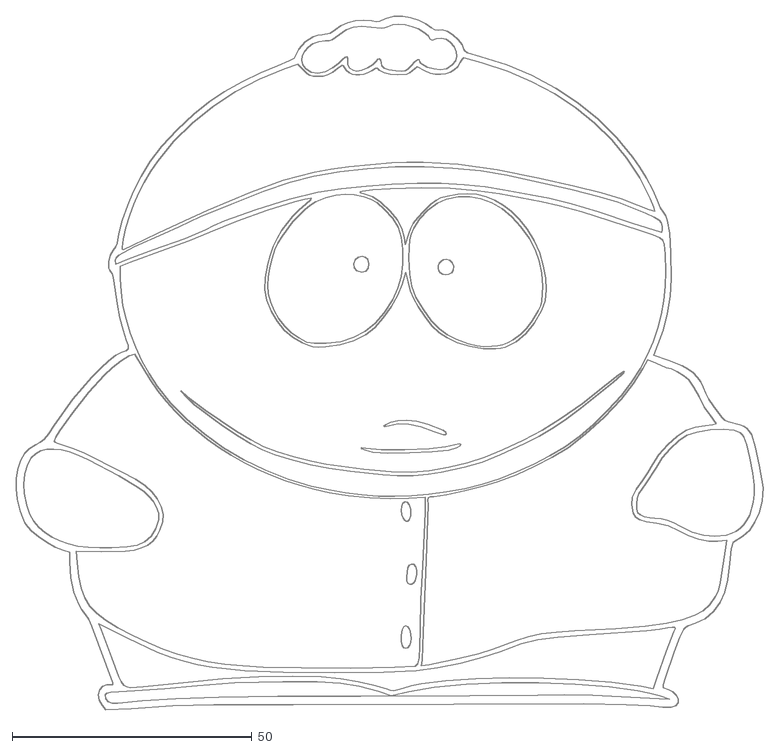
[picture p103: CAD file, 2023-11-14]
Dibujos_dxf/cartman.dxf
155.7 x 144.6
