impatrq/cnc_drawing_machine/Dibujos_dxf/nike.dxf

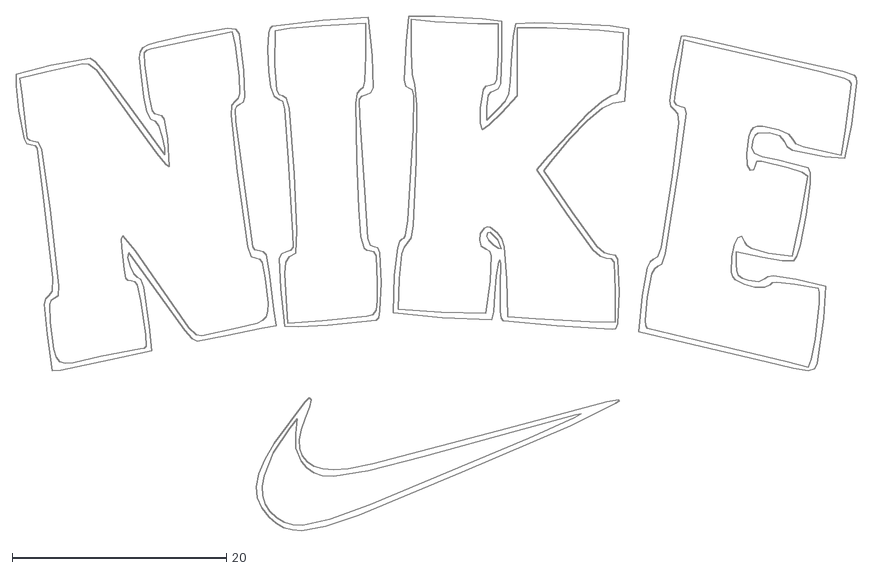
[picture p104: CAD file, 2023-11-14]
Dibujos_dxf/nike.dxf
78.5 x 48.0
