impatrq/cnc_drawing_machine/Dibujos_dxf/pika.dxf

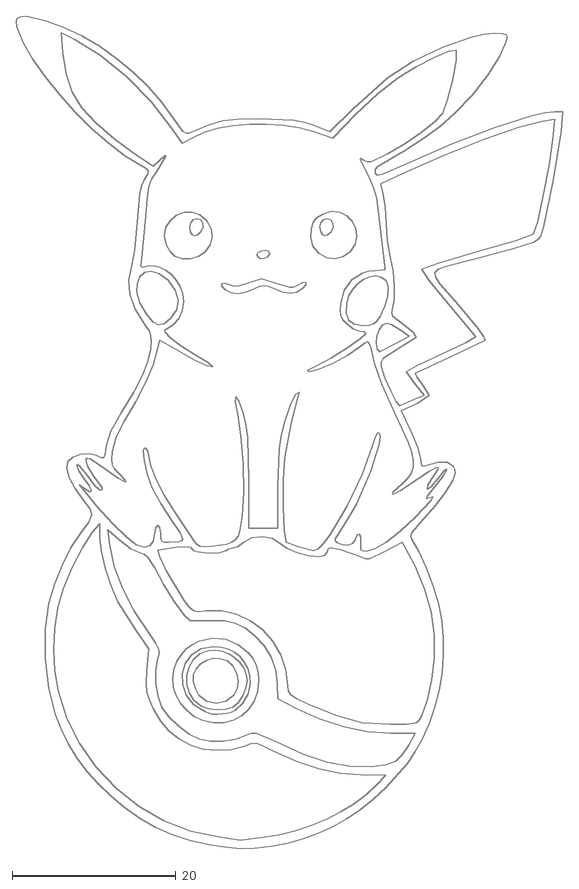
[picture p105: CAD file, 2023-11-14]
Dibujos_dxf/pika.dxf
66.7 x 101.5
