impatrq/cnc_drawing_machine/Dibujos_dxf/quito.dxf

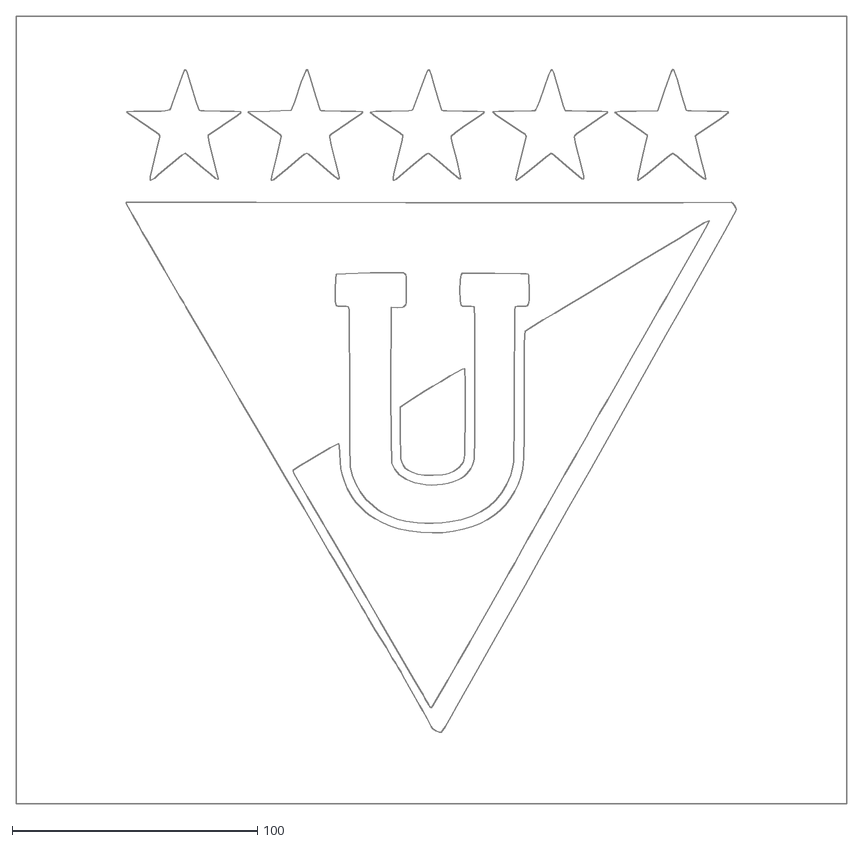
[picture p106: CAD file, 2023-11-14]
Dibujos_dxf/quito.dxf
338.7 x 321.2
