impatrq/cnc_drawing_machine/Dibujos_dxf/jordan.dxf

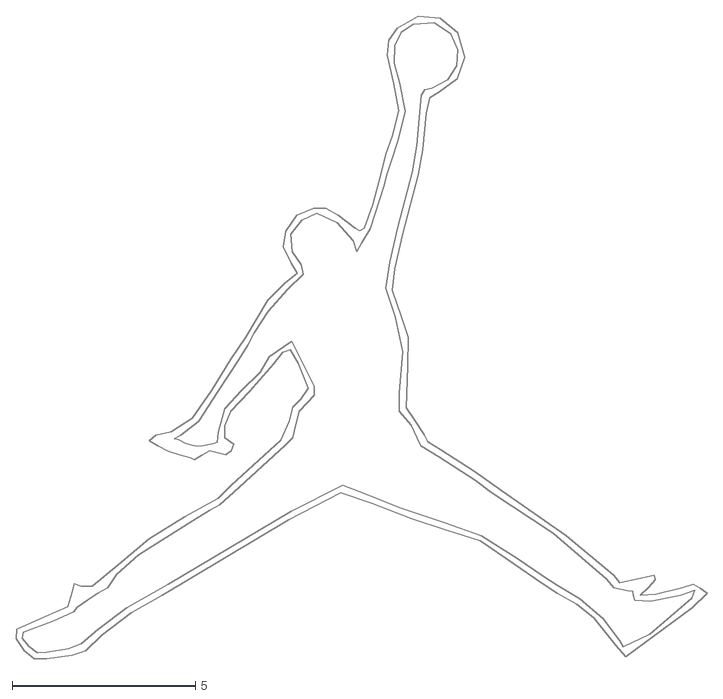
[picture p107: CAD file, 2023-11-14]
Dibujos_dxf/jordan.dxf
18.9 x 17.5
