impatrq/cnc_drawing_machine/Dibujos_dxf/Escudo_de_Racing_Club.dxf

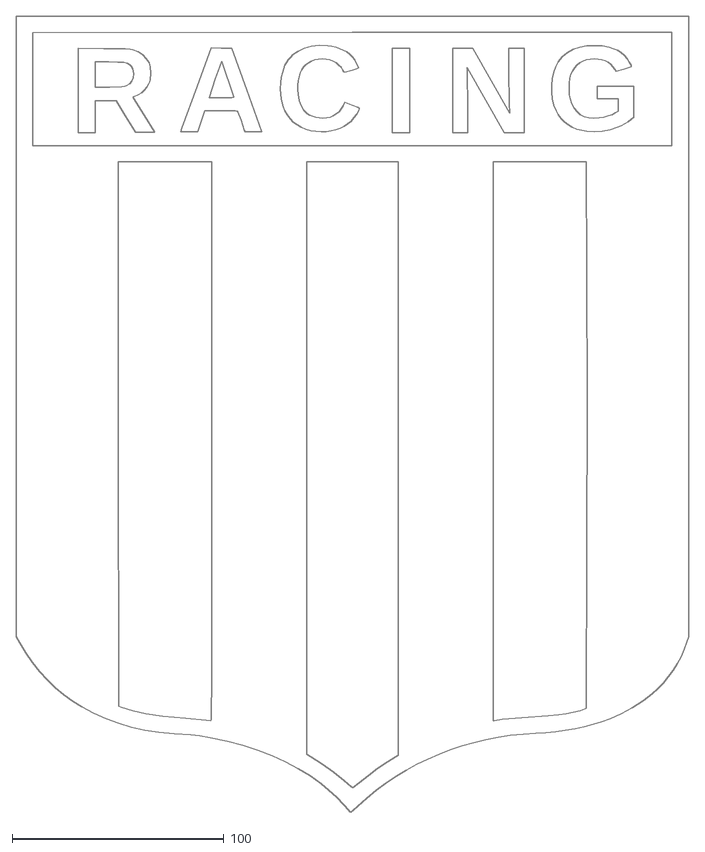
[picture p108: CAD file, 2023-11-14]
Dibujos_dxf/Escudo_de_Racing_Club.dxf
317.5 x 376.0
