impatrq/cnc_drawing_machine/Dibujos_dxf/spreen.dxf

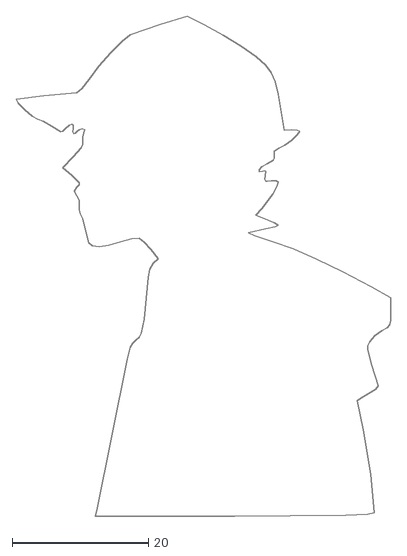
[picture p109: CAD file, 2023-11-14]
Dibujos_dxf/spreen.dxf
55.0 x 73.4
