impatrq/cnc_drawing_machine/Dibujos_dxf/copa del mundo.dxf

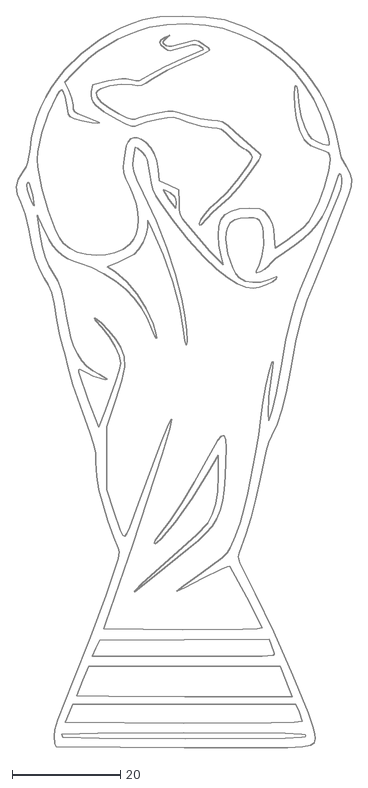
[picture p110: CAD file, 2023-11-14]
Dibujos_dxf/copa del mundo.dxf
61.9 x 135.3
