impatrq/cnc_drawing_machine/Dibujos_dxf/dragon.dxf

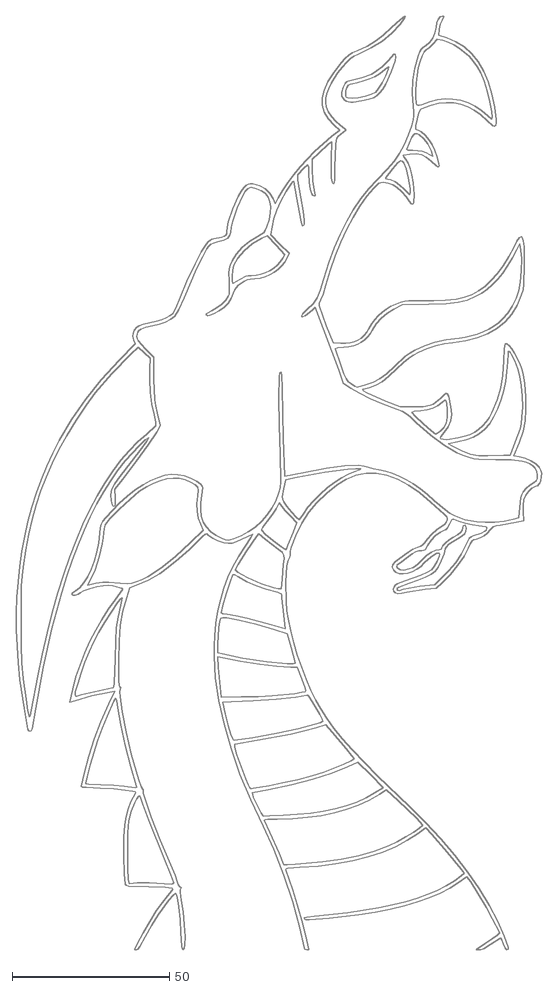
[picture p111: CAD file, 2023-11-14]
Dibujos_dxf/dragon.dxf
167.0 x 297.0
