impatrq/cnc_drawing_machine/Dibujos_dxf/homer.dxf

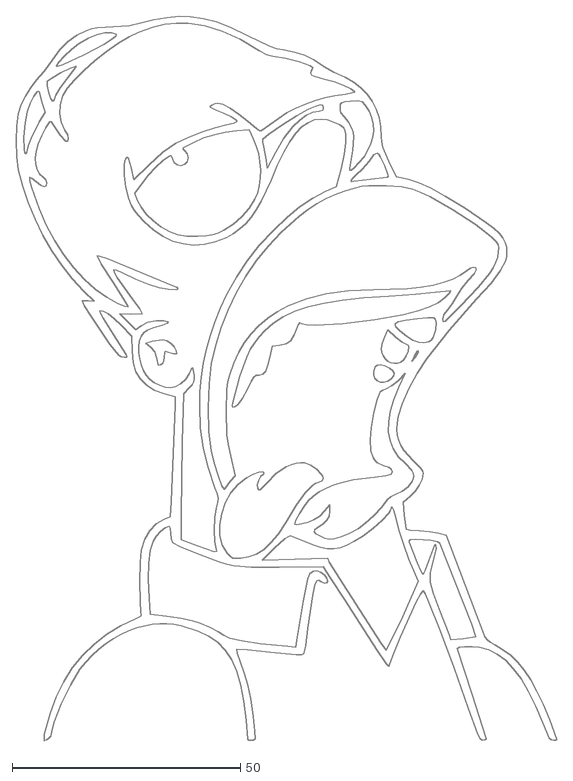
[picture p112: CAD file, 2023-11-14]
Dibujos_dxf/homer.dxf
118.5 x 158.7
