impatrq/cnc_drawing_machine/Dibujos_dxf/avengers.dxf

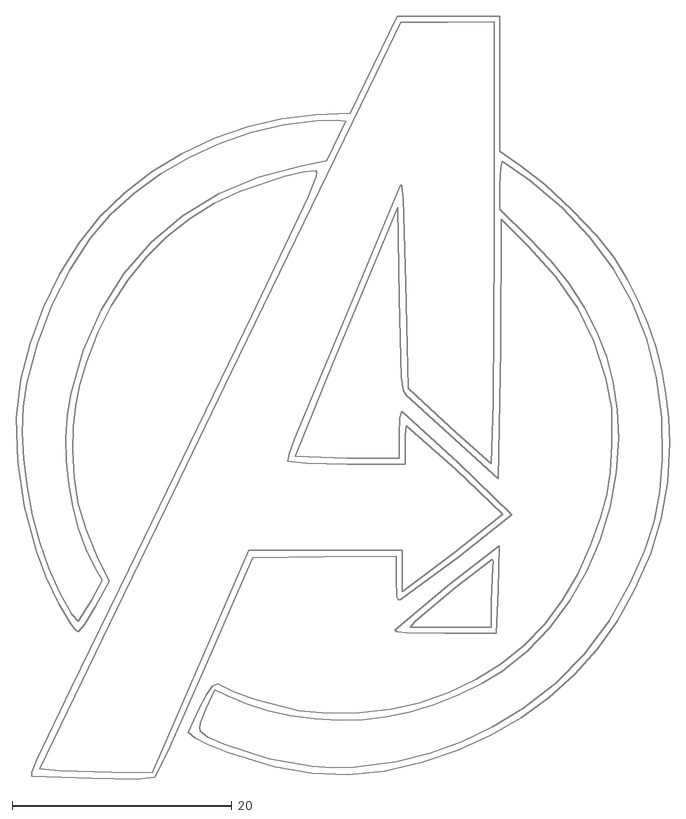
[picture p113: CAD file, 2023-11-14]
Dibujos_dxf/avengers.dxf
59.5 x 69.5
