impatrq/cnc_drawing_machine/Dibujos_dxf/impa2.dxf

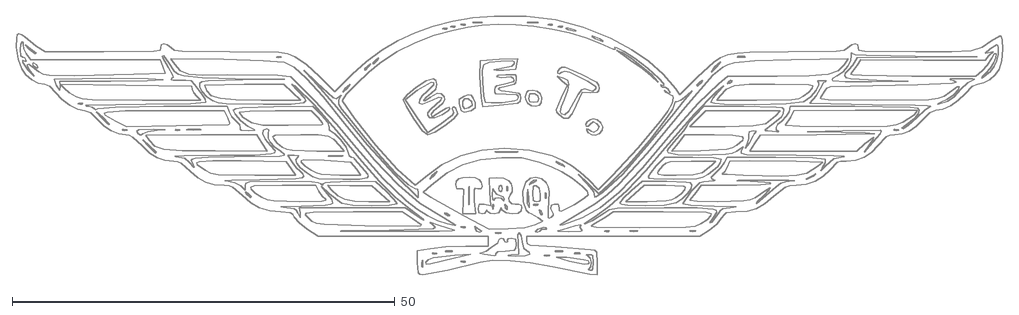
[picture p114: CAD file, 2023-11-14]
Dibujos_dxf/impa2.dxf
128.8 x 33.8
