impatrq/cnc_drawing_machine/Dibujos_dxf/ghostbusters.dxf

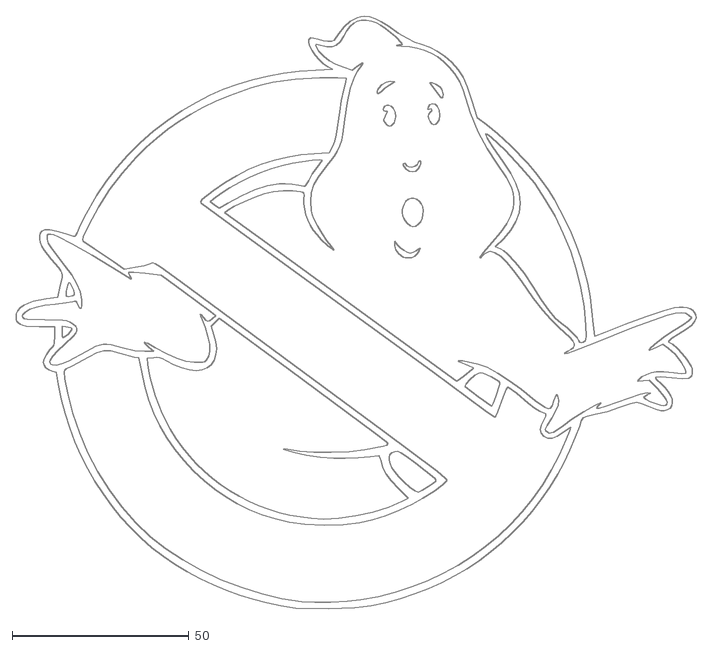
[picture p115: CAD file, 2023-11-14]
Dibujos_dxf/ghostbusters.dxf
192.6 x 167.7
