impatrq/cnc_drawing_machine/Dibujos_dxf/flu.dxf

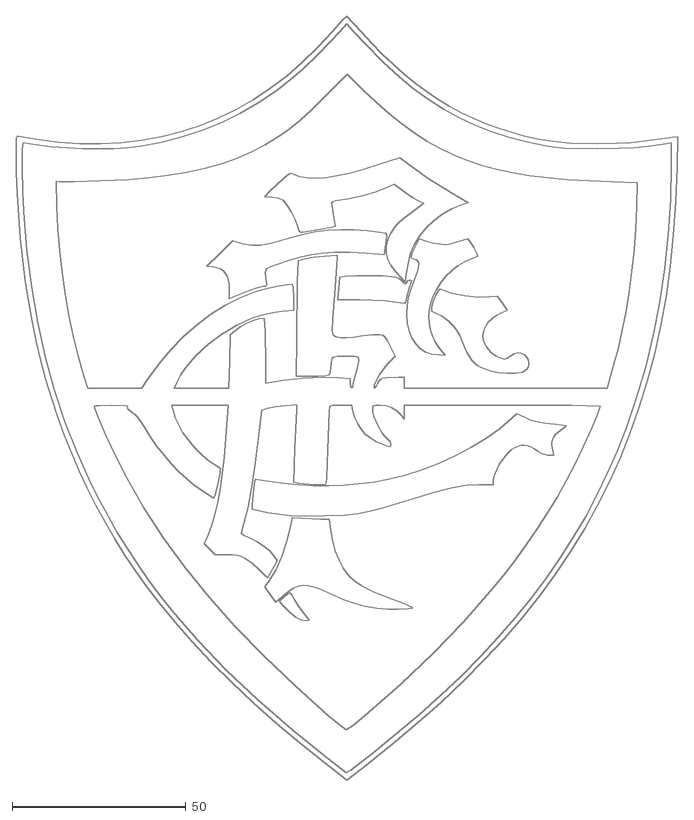
[picture p116: CAD file, 2023-11-14]
Dibujos_dxf/flu.dxf
190.6 x 220.0
