impatrq/cnc_drawing_machine/Dibujos_dxf/porche.dxf

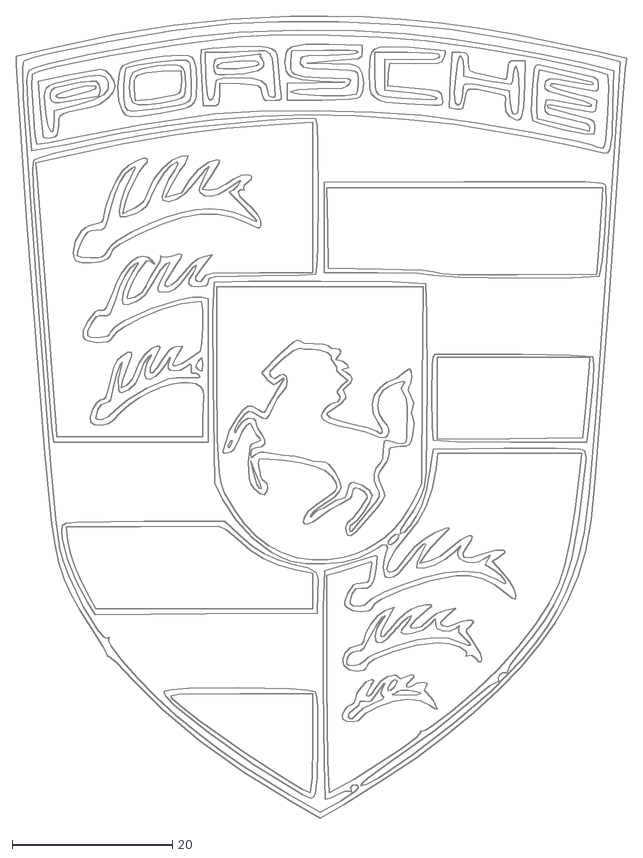
[picture p117: CAD file, 2023-11-14]
Dibujos_dxf/porche.dxf
76.2 x 100.1
