impatrq/cnc_drawing_machine/Dibujos_dxf/inter.dxf

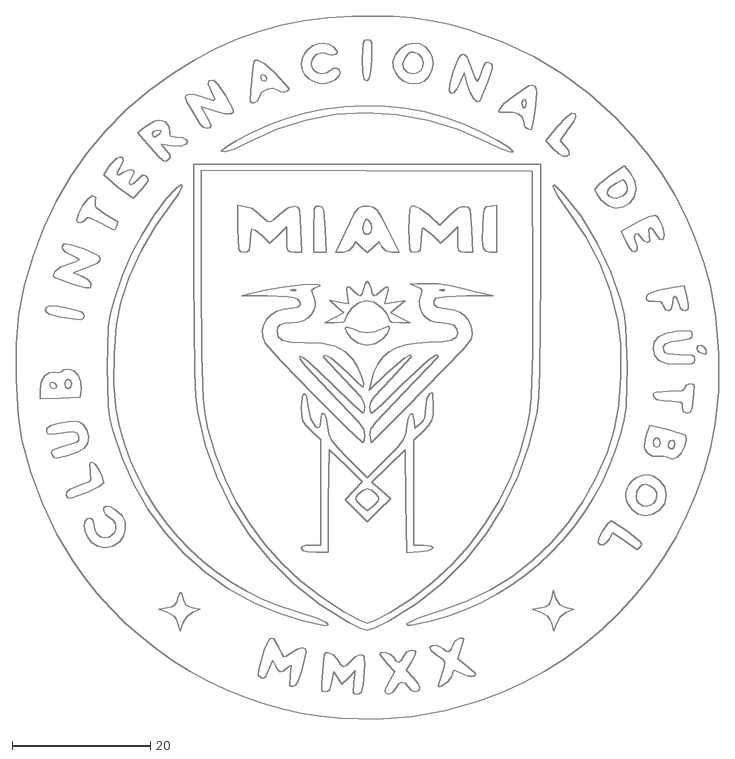
[picture p118: CAD file, 2023-11-14]
Dibujos_dxf/inter.dxf
101.5 x 101.6
