impatrq/cnc_drawing_machine/Calibracion Motores Mach3/eje x calibration.jpg

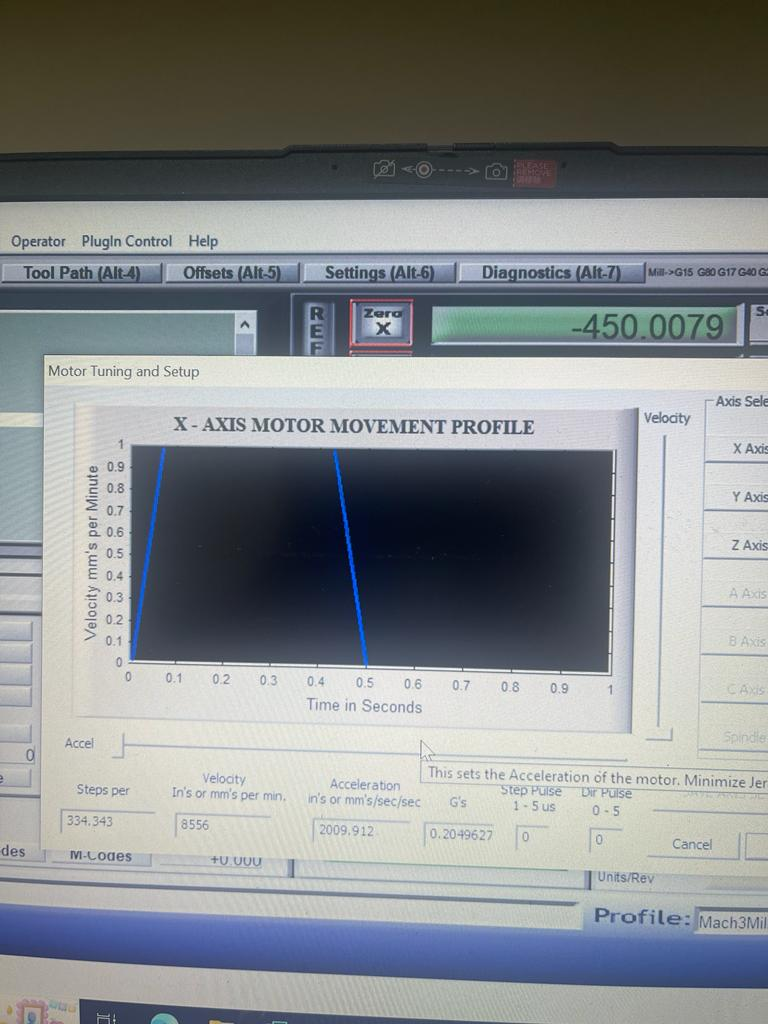
Calibracion Motores Mach3/eje x calibration.jpg
