impatrq/cnc_drawing_machine/Calibracion Motores Mach3/eje_z_calibration.jpg

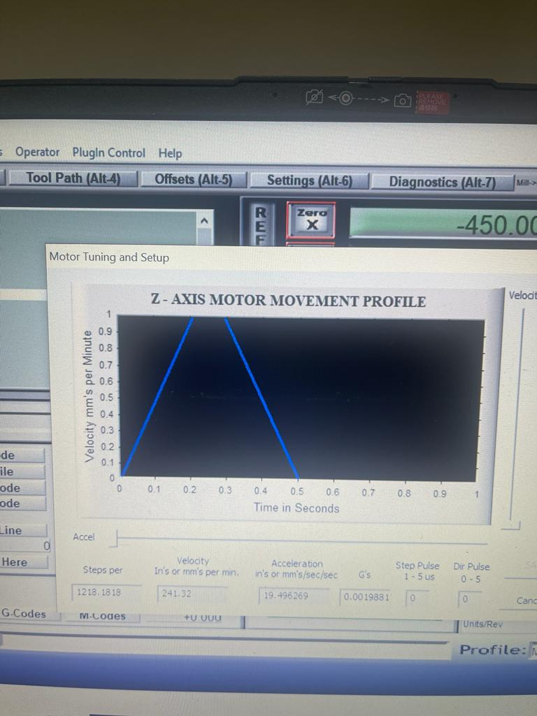
Calibracion Motores Mach3/eje_z_calibration.jpg
