impatrq/cnc_drawing_machine/Calibracion Motores Mach3/pins_motores_mach3.PNG

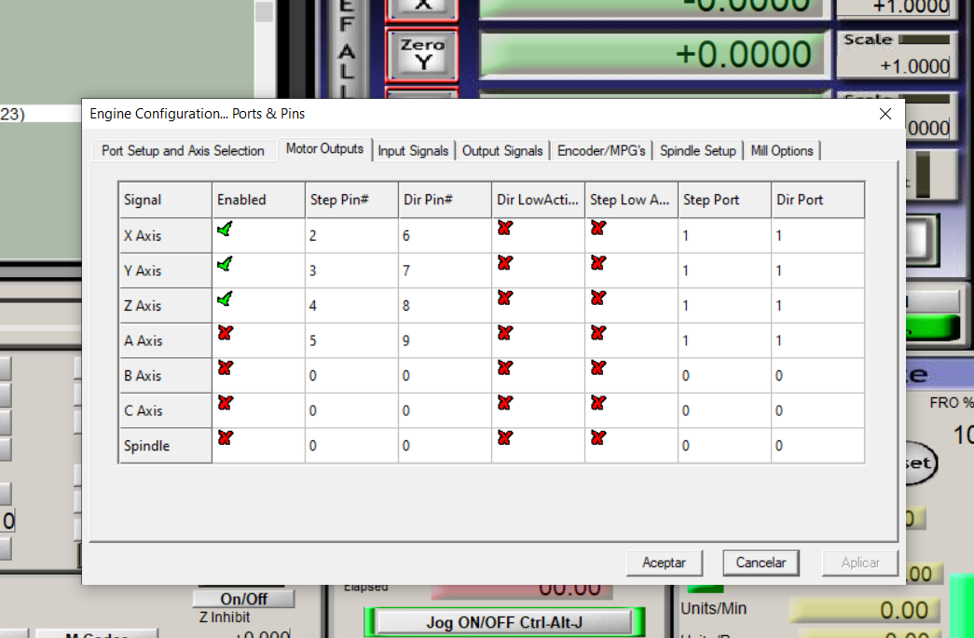
Calibracion Motores Mach3/pins_motores_mach3.PNG
